AresValley/ENIGMA/rotors/400009/README.md

<!-- PROJECT LOGO -->
<p align="center">
  <a href="https://github.com/AresValley/ENIGMA">
    
  </a>
</p>

<!-- ABOUT THE PROJECT -->
## Center Toothed Wheel - 400 009

**ID:** 400009 <br/>
**Material:** [PA6](https://github.com/AresValley/ENIGMA#pa6-) <br/>
**Weight:** 34.5 g <br/>
**A360:** https://a360.co/4fqHECO <br/>

### Blueprint
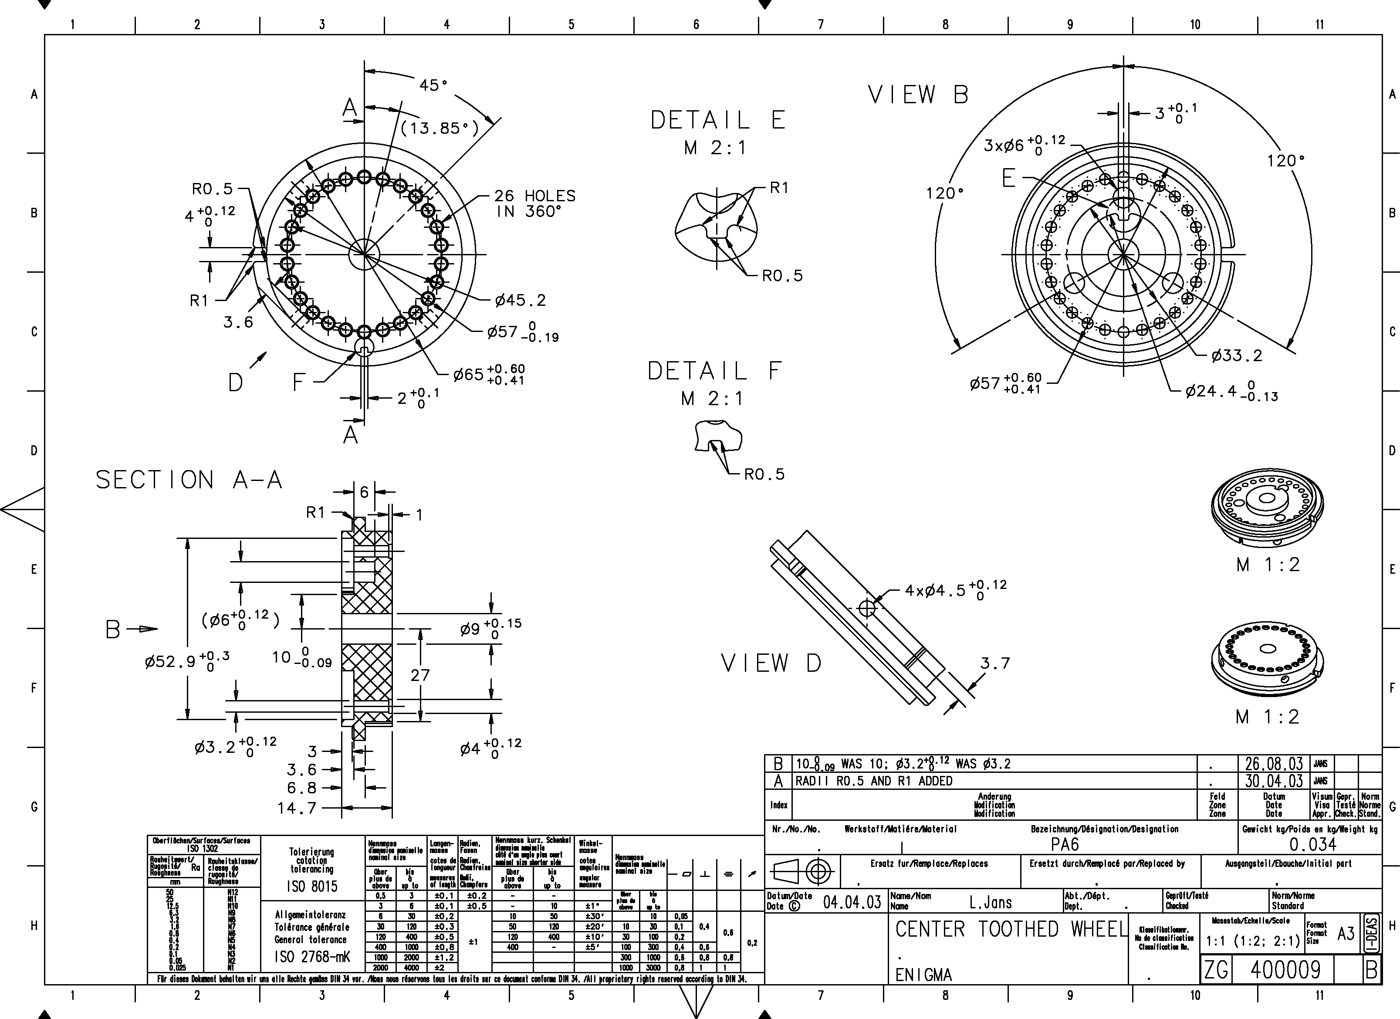
[picture p27: rotors/400009/BP.png]
Blueprint
