AresValley/ENIGMA/rotors/400012/README.md

<!-- PROJECT LOGO -->
<p align="center">
  <a href="https://github.com/AresValley/ENIGMA">
    
  </a>
</p>

<!-- ABOUT THE PROJECT -->
## STEEL BUSHING - 400 012

**ID:** 400012 <br/>
**Material:** [S235JR](https://github.com/AresValley/ENIGMA#s235jr-) <br/>
**Weight:** 8.37 g <br/>
**A360:** https://a360.co/3UYaBhf <br/>

### Blueprint
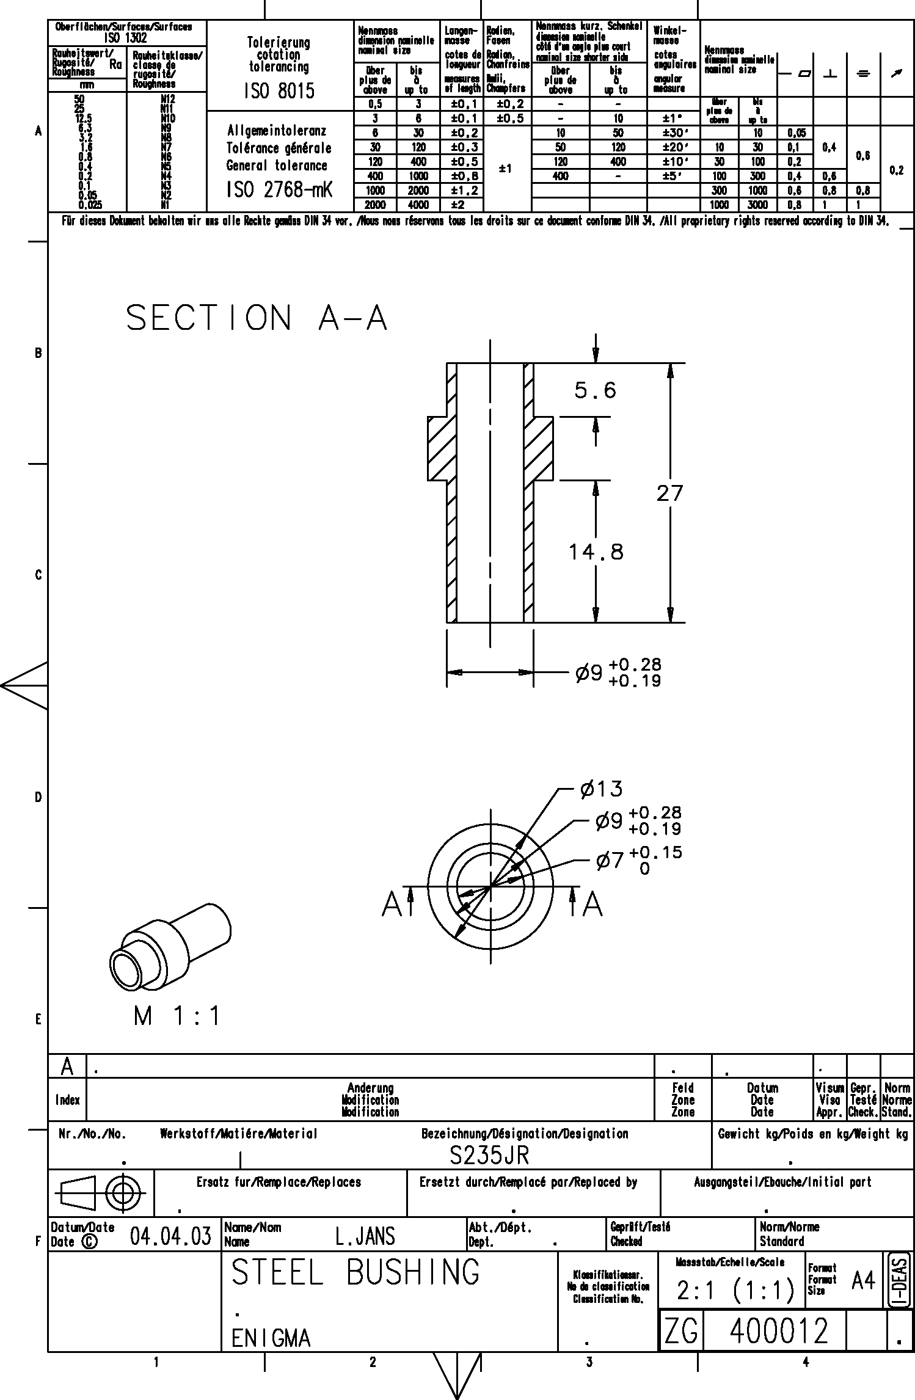
[picture p28: rotors/400012/BP.png]
