AresValley/ENIGMA/rack/100001/README.md

<!-- PROJECT LOGO -->
<p align="center">
  <a href="https://github.com/AresValley/ENIGMA">
    
  </a>
</p>

<!-- ABOUT THE PROJECT -->
## BEARING BLOCK LEFT - 100 001

**ID:** 100001 <br/>
**Material:** [S235JR](https://github.com/AresValley/ENIGMA#s235jr-) <br/>
**Weight:** 0.155 Kg <br/>
**A360:** https://a360.co/2P5f7vf <br/>

### Blueprint
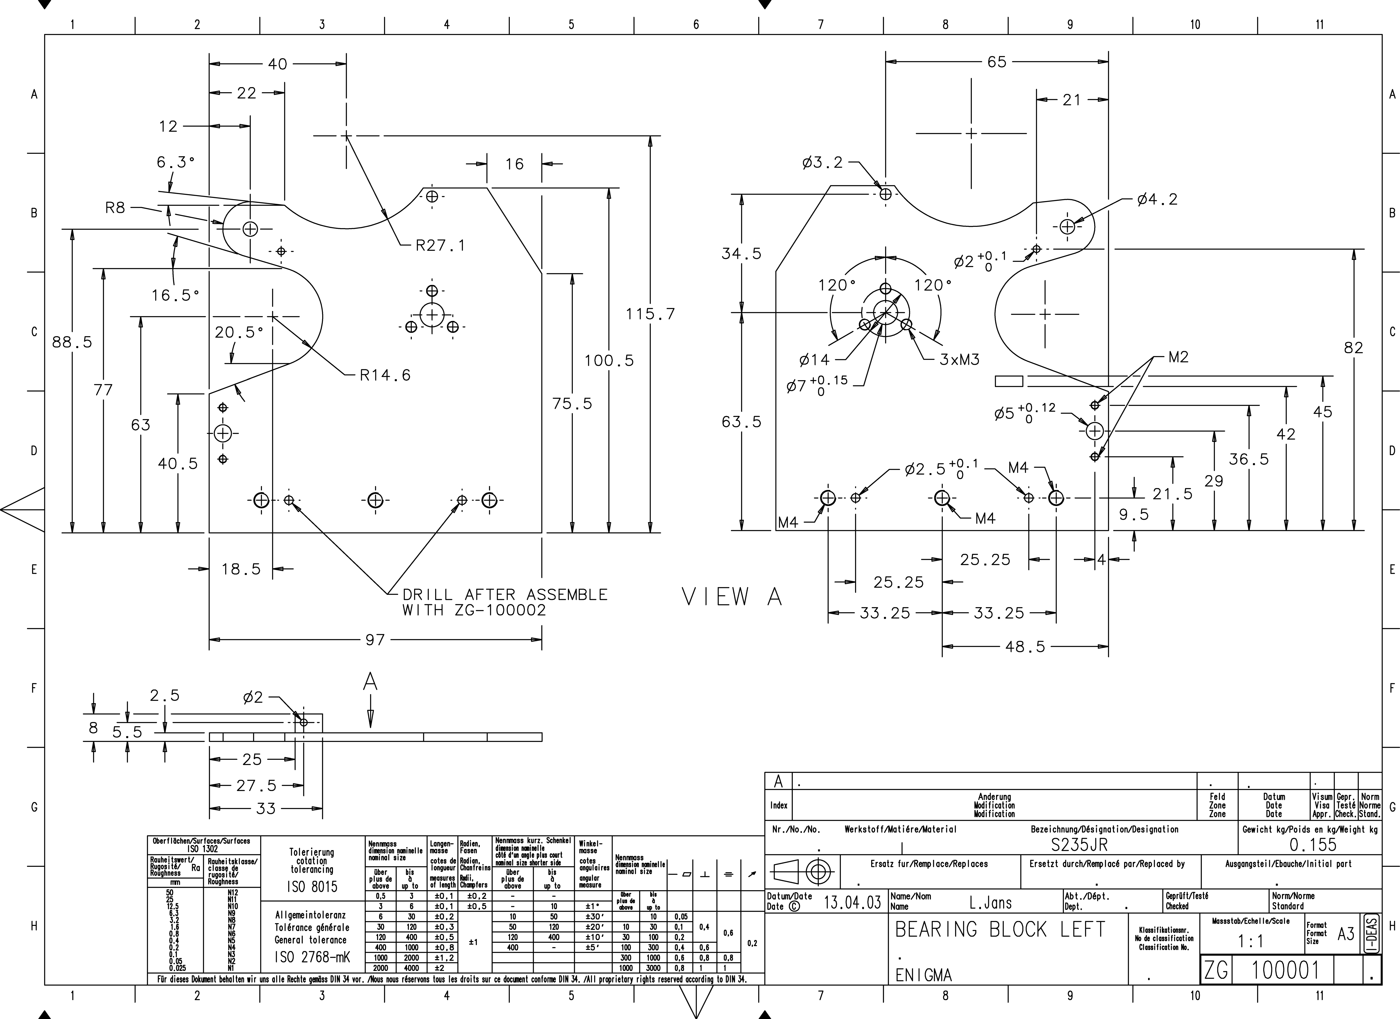
[picture p29: rack/100001/BP.png]
Blueprint
