AresValley/ENIGMA/rack/100005/README.md

<!-- PROJECT LOGO -->
<p align="center">
  <a href="https://github.com/AresValley/ENIGMA">
    
  </a>
</p>

<!-- ABOUT THE PROJECT -->
## SHAFT HOLDER - 100 005

**ID:** 100005 <br/>
**Material:** [S235JR](https://github.com/AresValley/ENIGMA#s235jr-) <br/>
**Weight:** 19.14 g <br/>
**A360:** https://a360.co/3PCjWI3 <br/>

### Blueprint
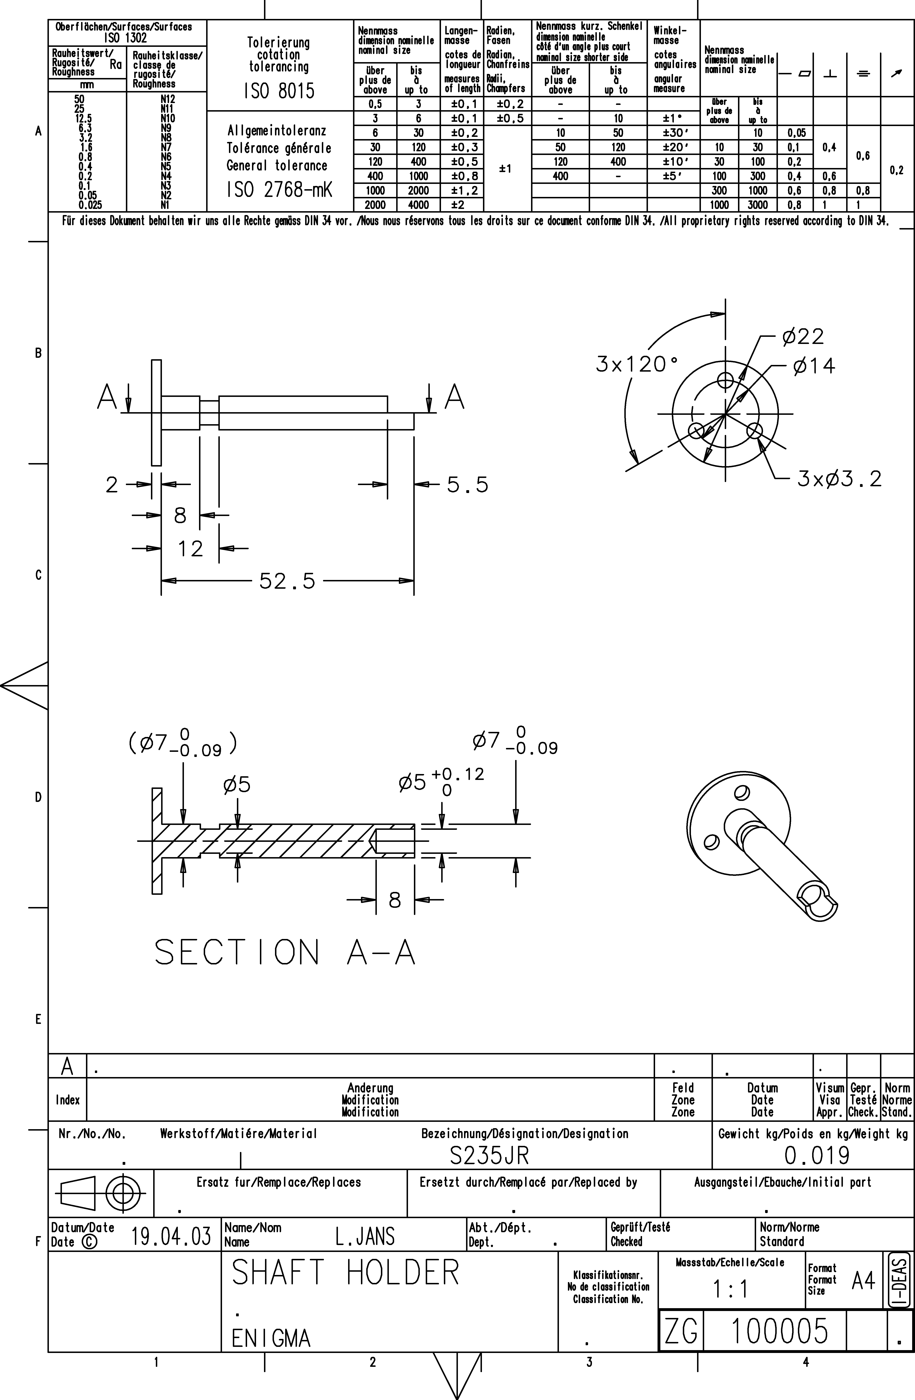
[picture p30: rack/100005/BP.png]
