AresValley/ENIGMA/rotors/400013/README.md

<!-- PROJECT LOGO -->
<p align="center">
  <a href="https://github.com/AresValley/ENIGMA">
    
  </a>
</p>

<!-- ABOUT THE PROJECT -->
## THREAD BUSHING - 400 013

**ID:** 400013 <br/>
**Material:** [S235JR](https://github.com/AresValley/ENIGMA#s235jr-) <br/>
**Weight:** 1.1 g <br/>
**A360:** https://a360.co/3PBEhyj <br/>

### Blueprint
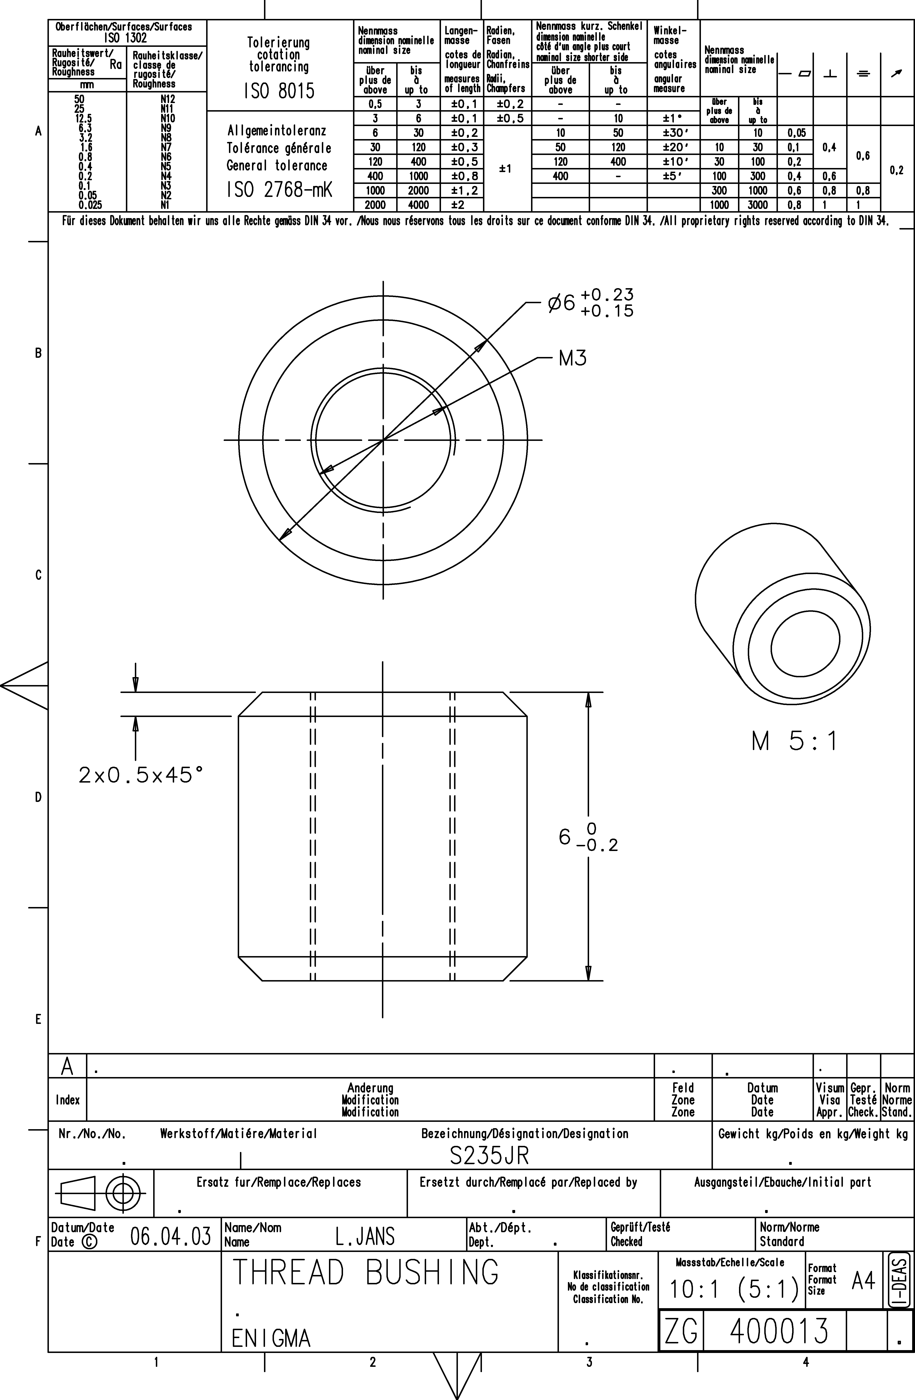
[picture p31: rotors/400013/BP.png]
