AresValley/ENIGMA/rotors/400017/README.md

<!-- PROJECT LOGO -->
<p align="center">
  <a href="https://github.com/AresValley/ENIGMA">
    
  </a>
</p>

<!-- ABOUT THE PROJECT -->
## SPRING - 400 017

**ID:** 400017 <br/>
**Material:** [CuZn40](https://github.com/AresValley/ENIGMA#cuzn40-) <br/>
**Weight:** 0.02 g <br/>
**A360:** https://a360.co/3RgDBjn <br/>

### Blueprint
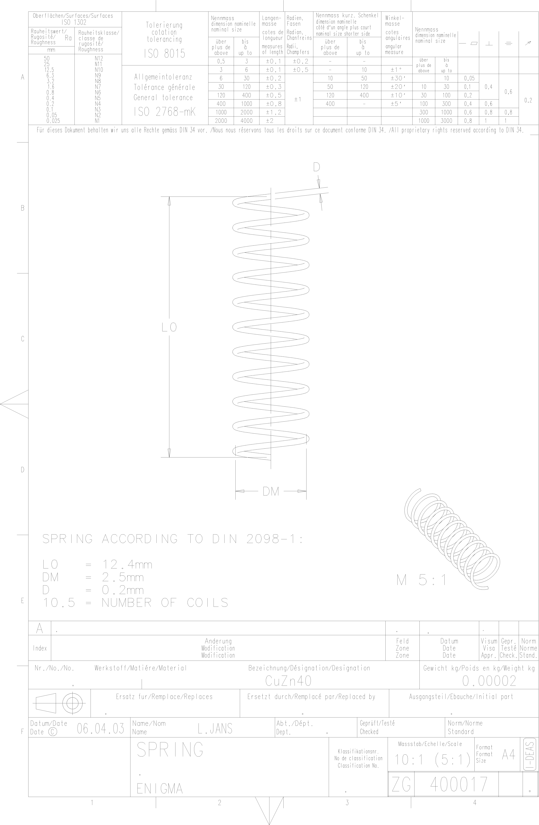
[picture p32: rotors/400017/BP.png]
