AresValley/ENIGMA/rotors/400019/README.md

<!-- PROJECT LOGO -->
<p align="center">
  <a href="https://github.com/AresValley/ENIGMA">
    
  </a>
</p>

<!-- ABOUT THE PROJECT -->
## THREAD BUSHING SMALL - 400 019

**ID:** 400019 <br/>
**Material:** [S235JR](https://github.com/AresValley/ENIGMA#s235jr-) <br/>
**Weight:** 0.38 g <br/>
**A360:** https://a360.co/45SvyxI <br/>

### Blueprint
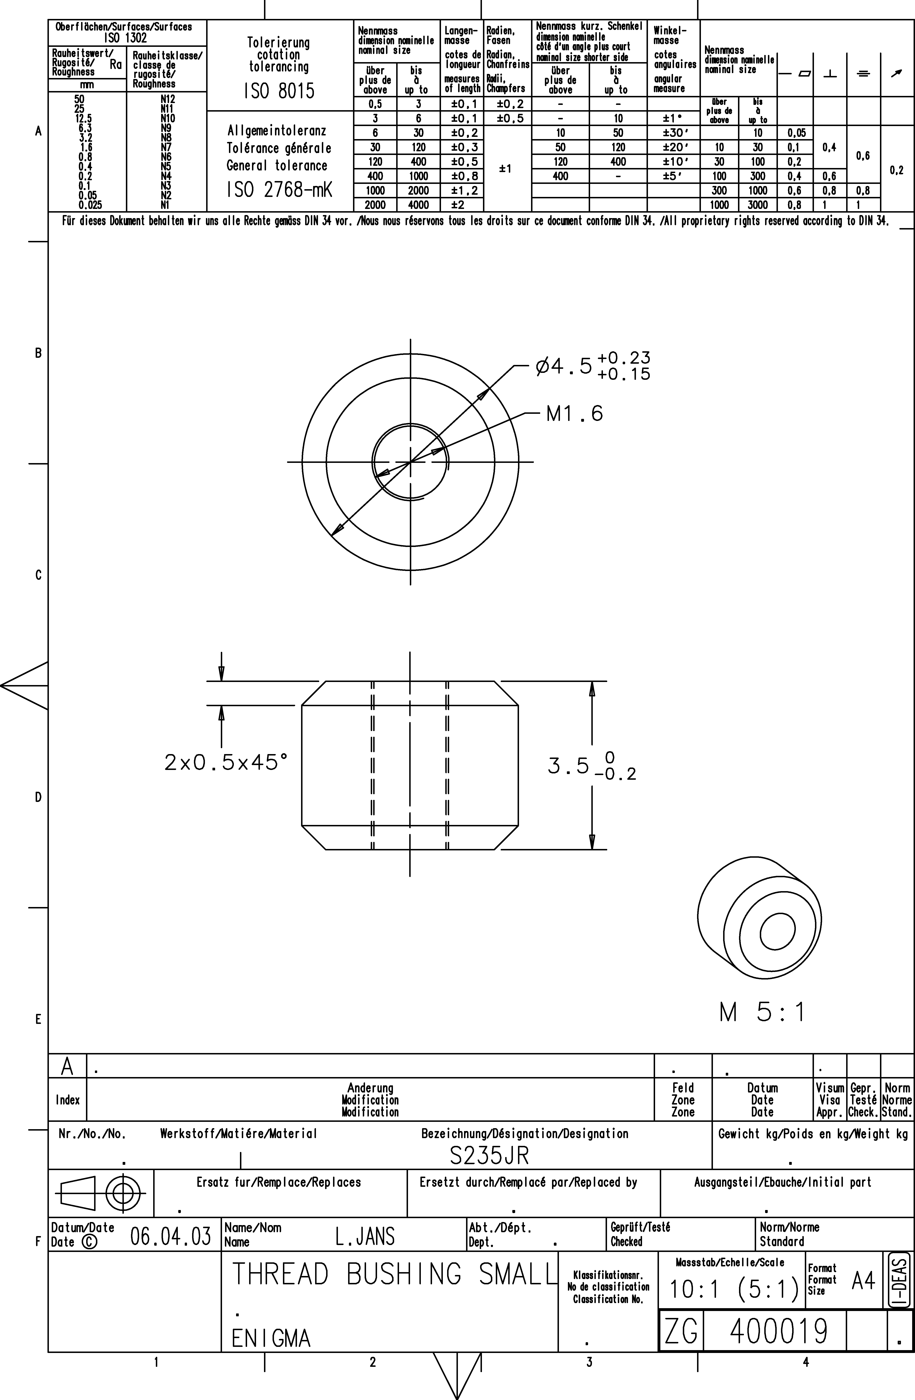
[picture p33: rotors/400019/BP.png]
