AresValley/ENIGMA/rotors/400001/README.md

<!-- PROJECT LOGO -->
<p align="center">
  <a href="https://github.com/AresValley/ENIGMA">
    
  </a>
</p>

<!-- ABOUT THE PROJECT -->
## KERFRING - 400 001

**ID:** 400001 <br/>
**Material:** [S235JR](https://github.com/AresValley/ENIGMA#s235jr-) <br/>
**Weight:** 0.0169 Kg <br/>
**A360:** https://a360.co/2ZTC5rj <br/>

### Blueprint
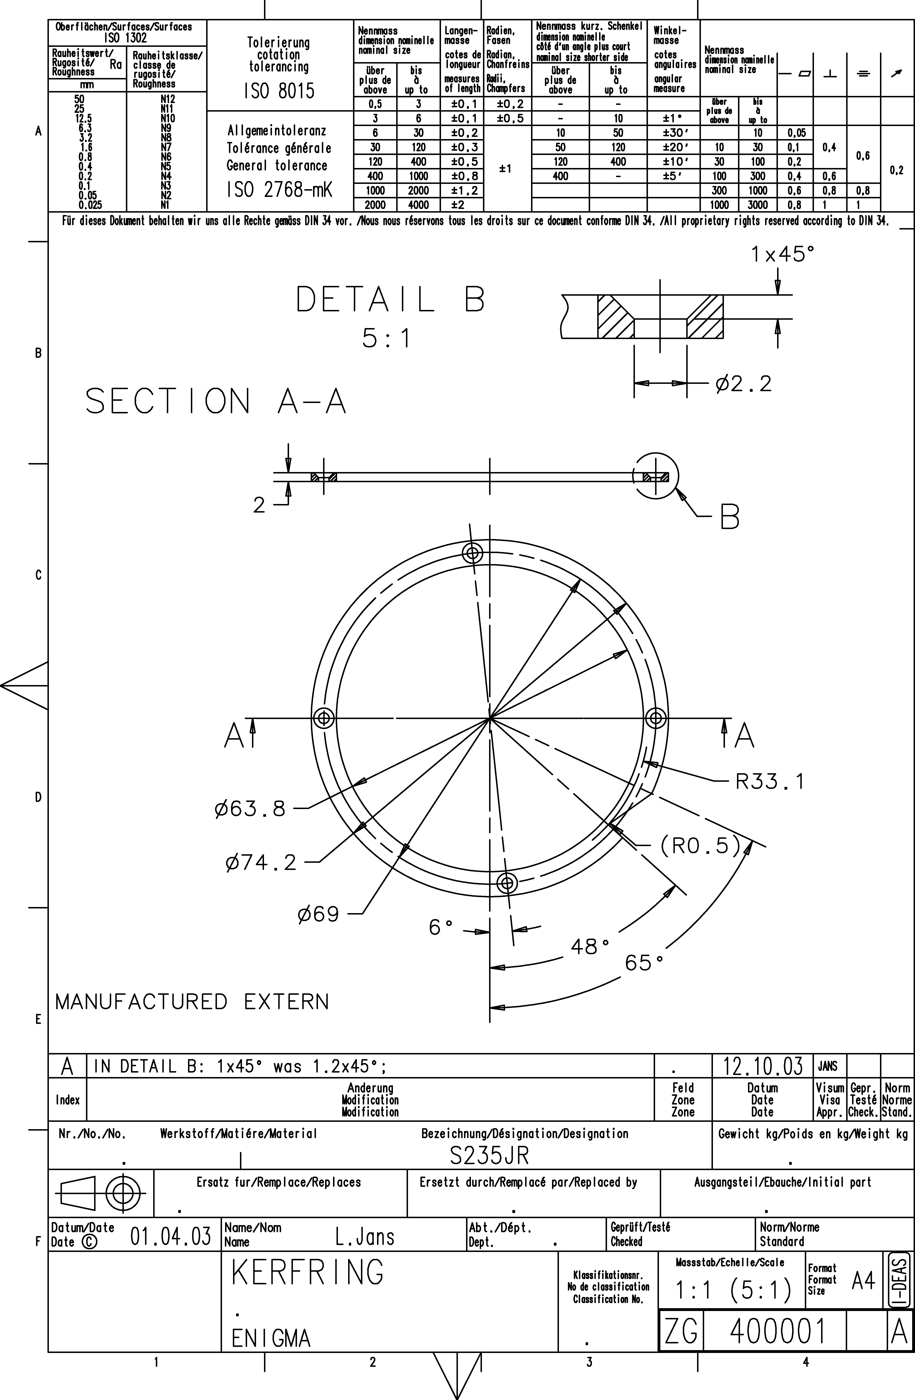
[picture p34: rotors/400001/BP.png]
