AresValley/ENIGMA/rotors/400002/README.md

<!-- PROJECT LOGO -->
<p align="center">
  <a href="https://github.com/AresValley/ENIGMA">
    
  </a>
</p>

<!-- ABOUT THE PROJECT -->
## DIGITRING - 400 002

**ID:** 400002 <br/>
**Material:** [S235JR](https://github.com/AresValley/ENIGMA#x12cr13-) <br/>
**Weight:** 0.113 Kg <br/>
**A360:** https://a360.co/3kyzwol <br/>

### Blueprint
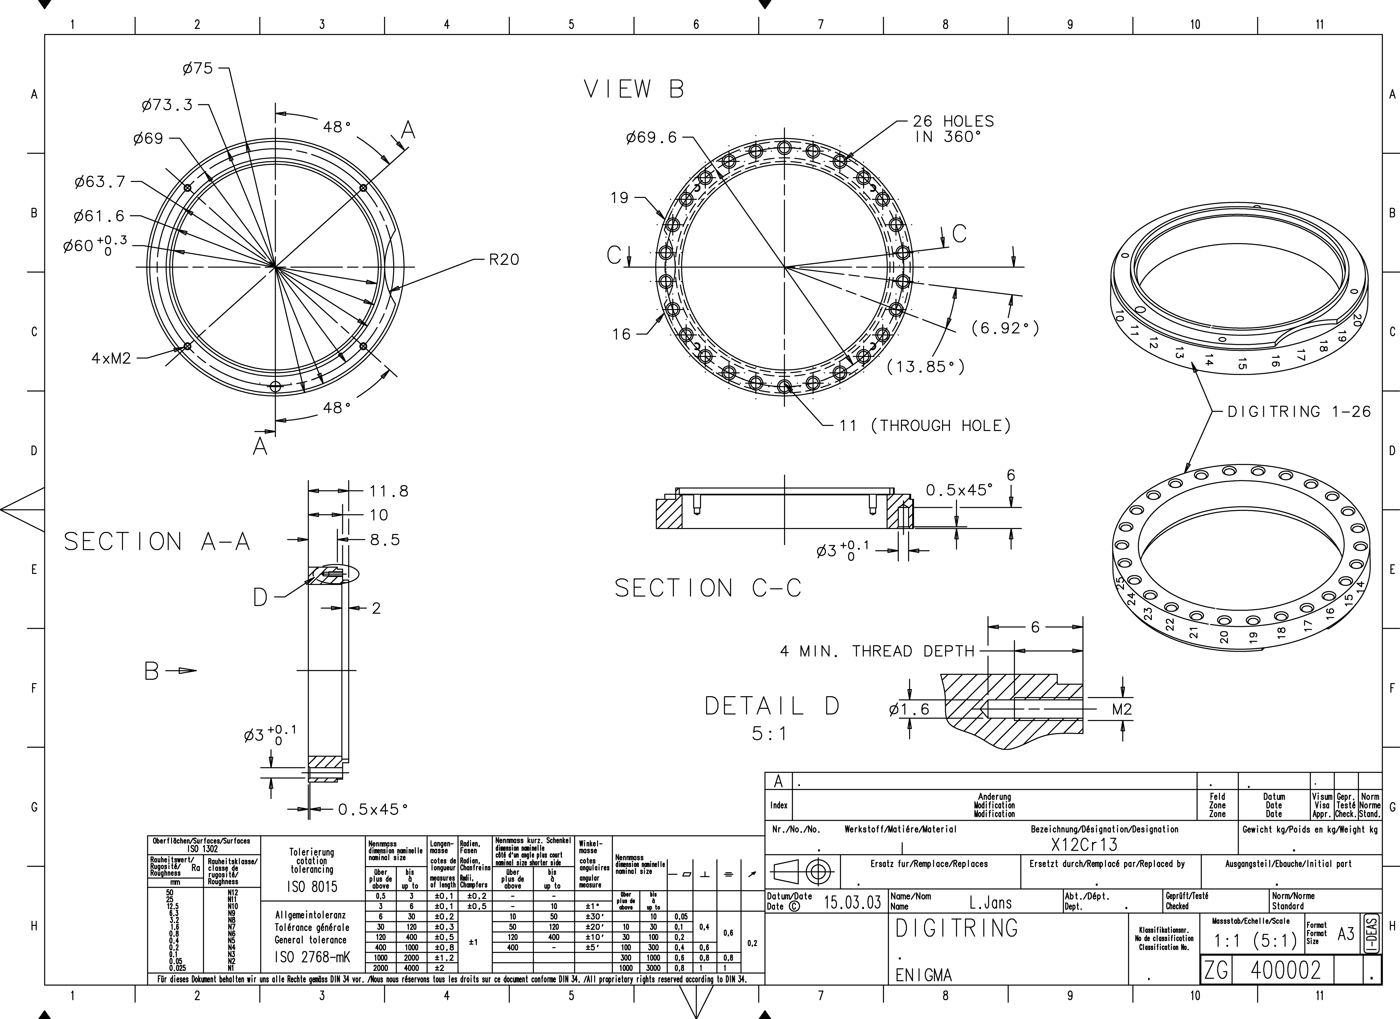
[picture p35: rotors/400002/BP.png]
