AresValley/ENIGMA/rotors/400003/README.md

<!-- PROJECT LOGO -->
<p align="center">
  <a href="https://github.com/AresValley/ENIGMA">
    
  </a>
</p>

<!-- ABOUT THE PROJECT -->
## BUSHING - 400 003

**ID:** 400003 <br/>
**Material:** [S235JR](https://github.com/AresValley/ENIGMA#s235jr-) <br/>
**Weight:** 0.054 Kg <br/>
**A360:** https://a360.co/3sJqWpV <br/>

### Blueprint
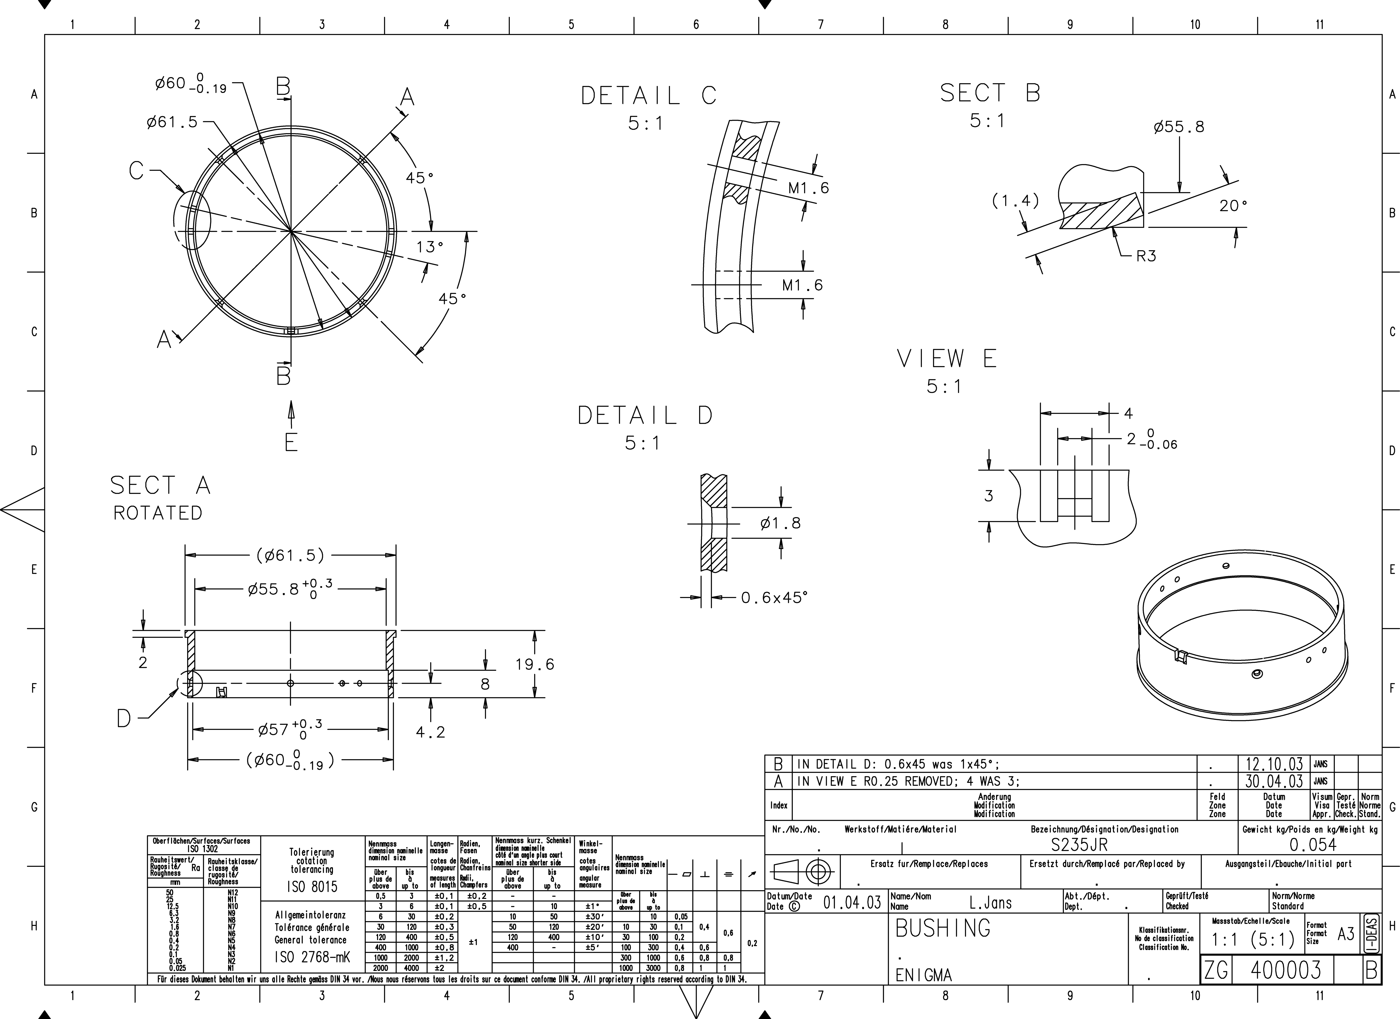
[picture p36: rotors/400003/BP.png]
