AresValley/ENIGMA/rotors/400004/README.md

<!-- PROJECT LOGO -->
<p align="center">
  <a href="https://github.com/AresValley/ENIGMA">
    
  </a>
</p>

<!-- ABOUT THE PROJECT -->
## ROLL SHAFT - 400 004

**ID:** 400004 <br/>
**Material:** [S235JR](https://github.com/AresValley/ENIGMA#s235jr-) <br/>
**Weight:** 0.0270 Kg <br/>
**A360:** https://a360.co/2NRQIZV <br/>

### Blueprint
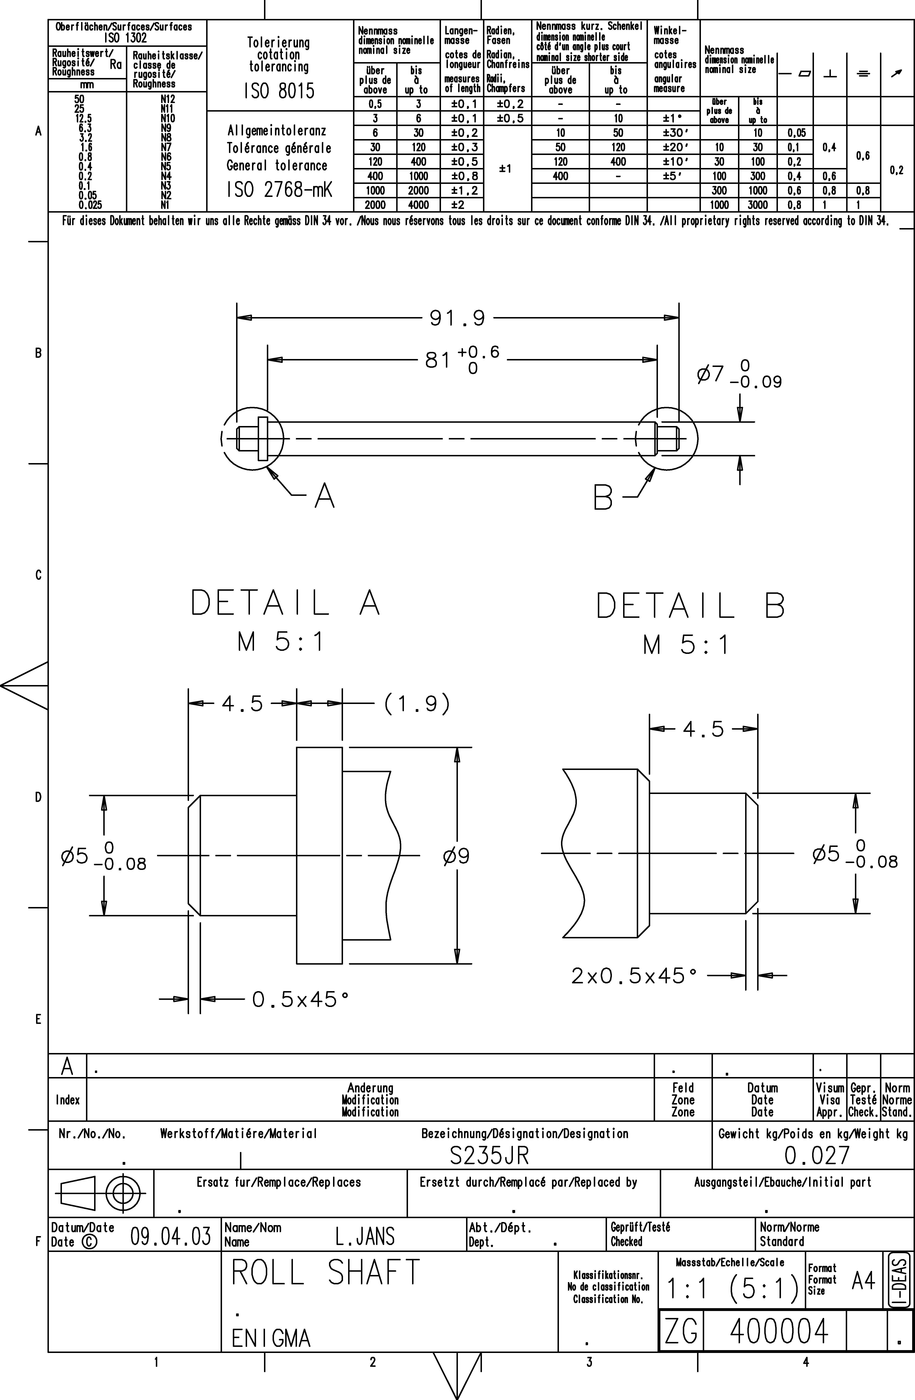
[picture p37: rotors/400004/BP.png]
