AresValley/ENIGMA/rotors/400005/README.md

<!-- PROJECT LOGO -->
<p align="center">
  <a href="https://github.com/AresValley/ENIGMA">
    
  </a>
</p>

<!-- ABOUT THE PROJECT -->
## BRACKET - 400 005

**ID:** 400005 <br/>
**Material:** [S235JR](https://github.com/AresValley/ENIGMA#s235jr-) <br/>
**Weight:** 0.0020 Kg <br/>
**A360:** https://a360.co/3lvvoXo <br/>

### Blueprint
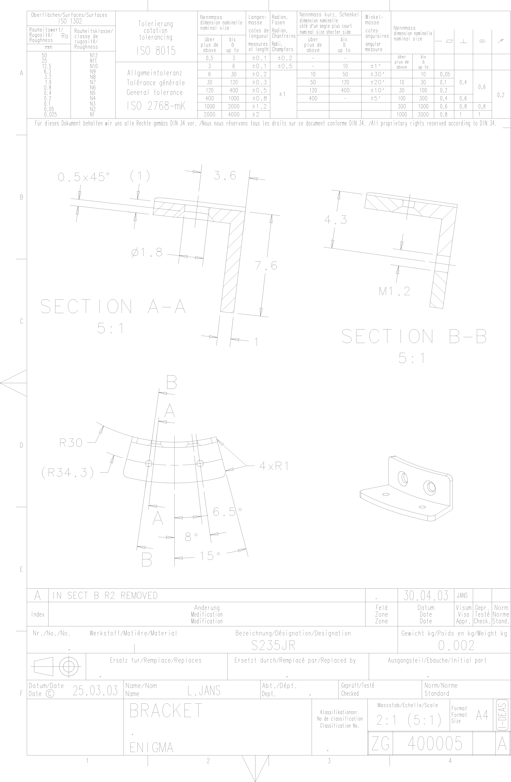
[picture p38: rotors/400005/BP.png]
