AresValley/ENIGMA/rotors/400006/README.md

<!-- PROJECT LOGO -->
<p align="center">
  <a href="https://github.com/AresValley/ENIGMA">
    
  </a>
</p>

<!-- ABOUT THE PROJECT -->
## CLAMP - 400 006

**ID:** 400006 <br/>
**Material:** [38Si7](https://github.com/AresValley/ENIGMA#38si7-) <br/>
**Weight:** 0.0013 Kg <br/>
**A360:** https://a360.co/3wWaZkC <br/>

### Blueprint
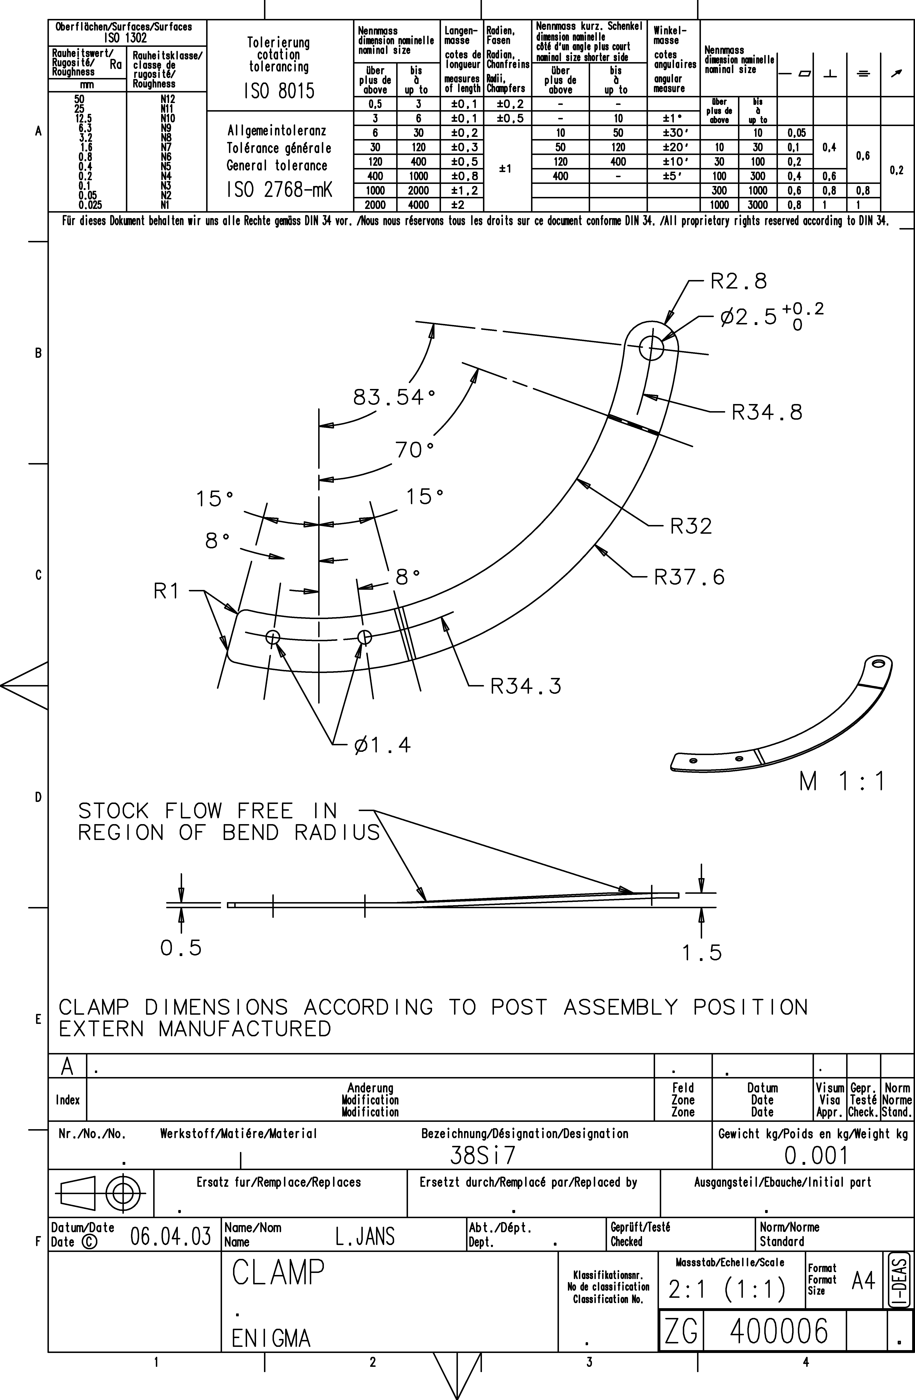
[picture p39: rotors/400006/BP.png]
