AresValley/ENIGMA/rotors/400007/README.md

<!-- PROJECT LOGO -->
<p align="center">
  <a href="https://github.com/AresValley/ENIGMA">
    
  </a>
</p>

<!-- ABOUT THE PROJECT -->
## PIN - 400 007

**ID:** 400007 <br/>
**Material:** [S235JR](https://github.com/AresValley/ENIGMA#s235jr-) <br/>
**Weight:** 0.0004 Kg <br/>
**A360:** https://a360.co/385FHOT <br/>

### Blueprint
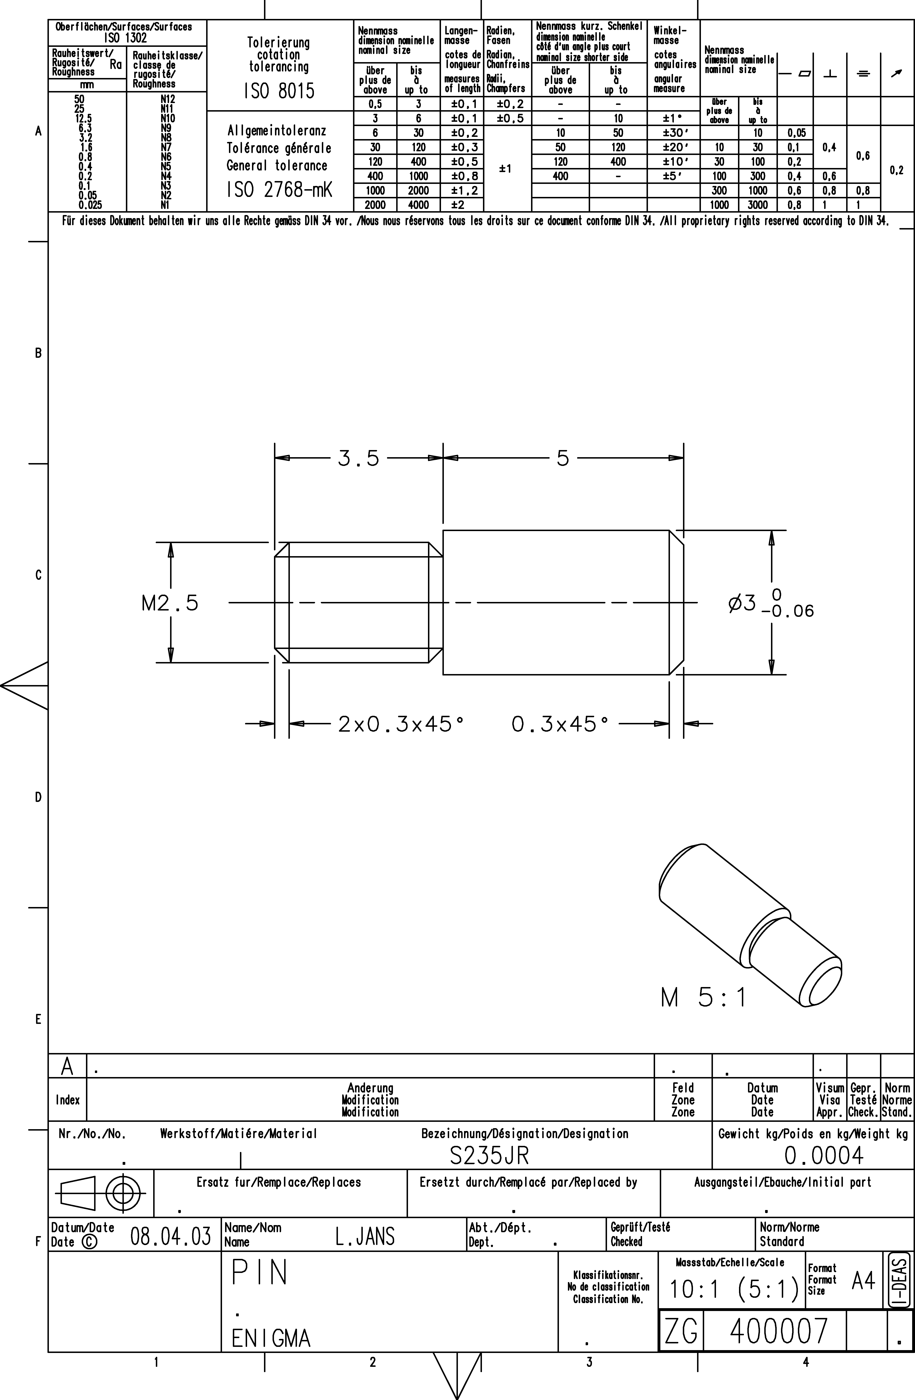
[picture p40: rotors/400007/BP.png]
