AresValley/ENIGMA/rotors/400011/README.md

<!-- PROJECT LOGO -->
<p align="center">
  <a href="https://github.com/AresValley/ENIGMA">
    
  </a>
</p>

<!-- ABOUT THE PROJECT -->
## ROLLPLATE - 400 011

**ID:** 400011 <br/>
**Material:** [PA6](https://github.com/AresValley/ENIGMA#pa6-) <br/>
**Weight:** 0.0090 Kg <br/>
**A360:** https://a360.co/3NFh4rl <br/>

### Blueprint
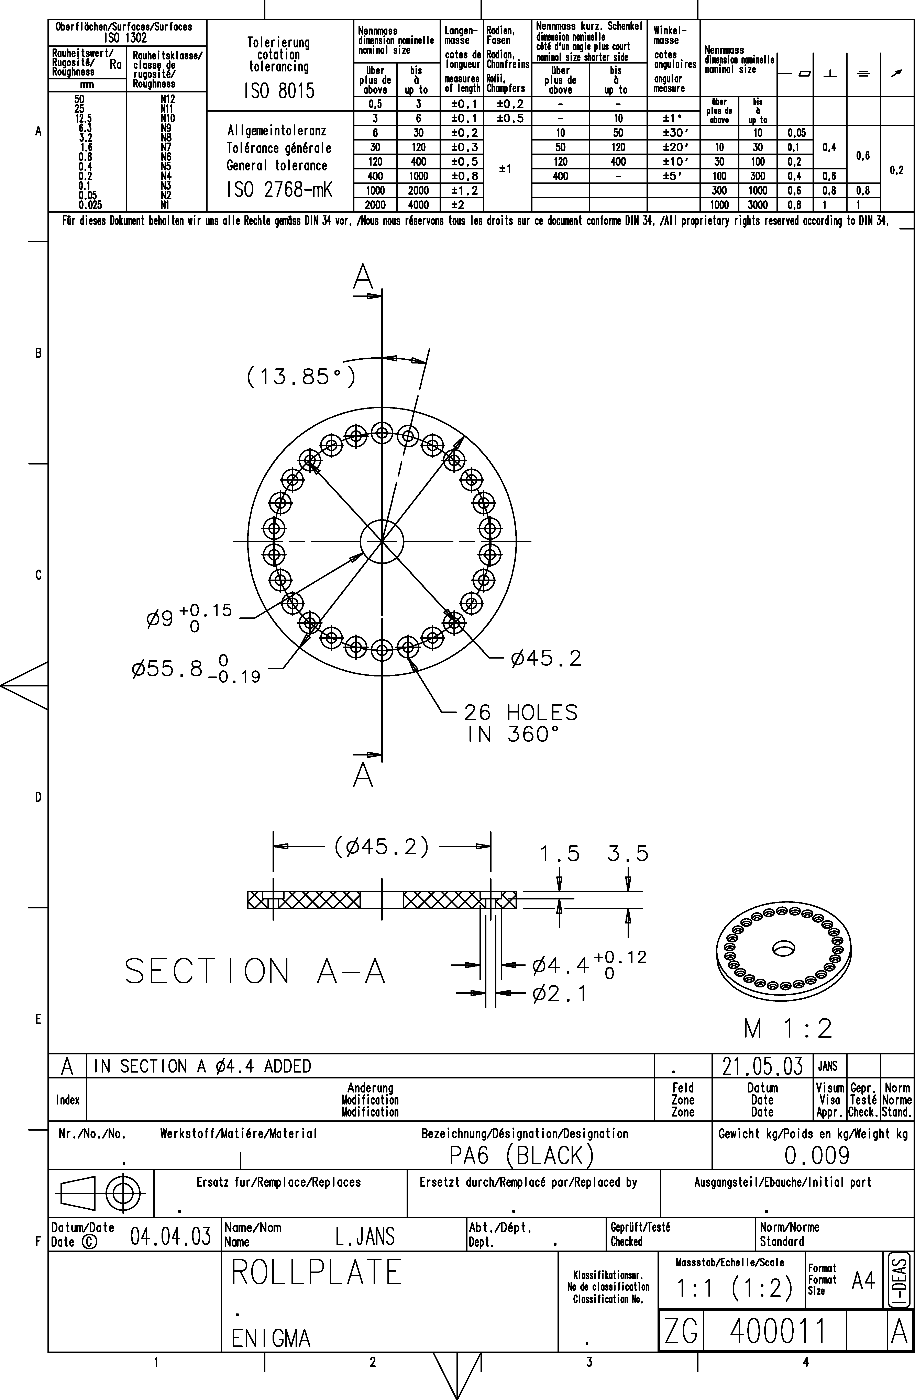
[picture p41: rotors/400011/BP.png]
