AresValley/ENIGMA/rotors/400014/README.md

<!-- PROJECT LOGO -->
<p align="center">
  <a href="https://github.com/AresValley/ENIGMA">
    
  </a>
</p>

<!-- ABOUT THE PROJECT -->
## THOOTED WHEEL - 400 014

**ID:** 400014 <br/>
**Material:** [S235JR](https://github.com/AresValley/ENIGMA#s235jr-) <br/>
**Weight:** 0.1140 Kg <br/>
**A360:** https://a360.co/38ouFV5 <br/>

### Blueprint
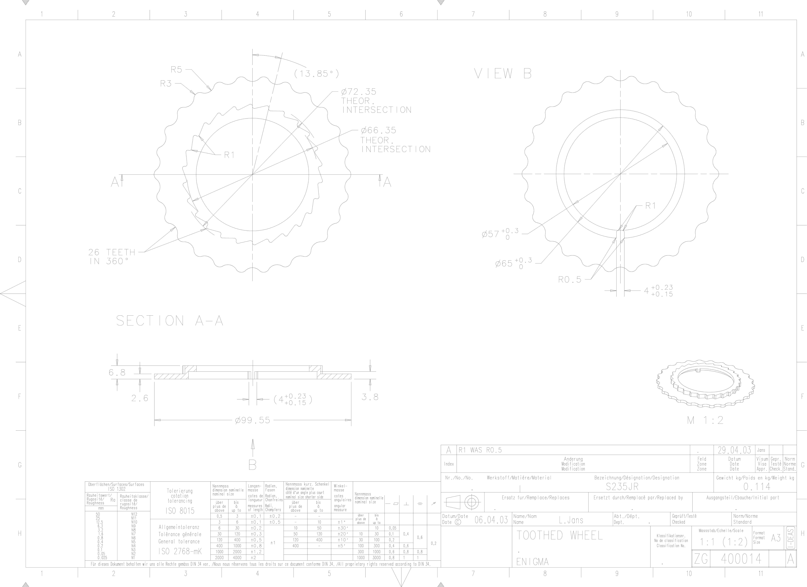
[picture p42: rotors/400014/BP.png]
