AresValley/ENIGMA/rotors/400016/README.md

<!-- PROJECT LOGO -->
<p align="center">
  <a href="https://github.com/AresValley/ENIGMA">
    
  </a>
</p>

<!-- ABOUT THE PROJECT -->
## CONTACT PIN - 400 016

**ID:** 400016 <br/>
**Material:** [CuZn40](https://github.com/AresValley/ENIGMA#cuzn40-) <br/>
**Weight:** 0.0003 Kg <br/>
**A360:** https://a360.co/3pN8evb <br/>

### Blueprint
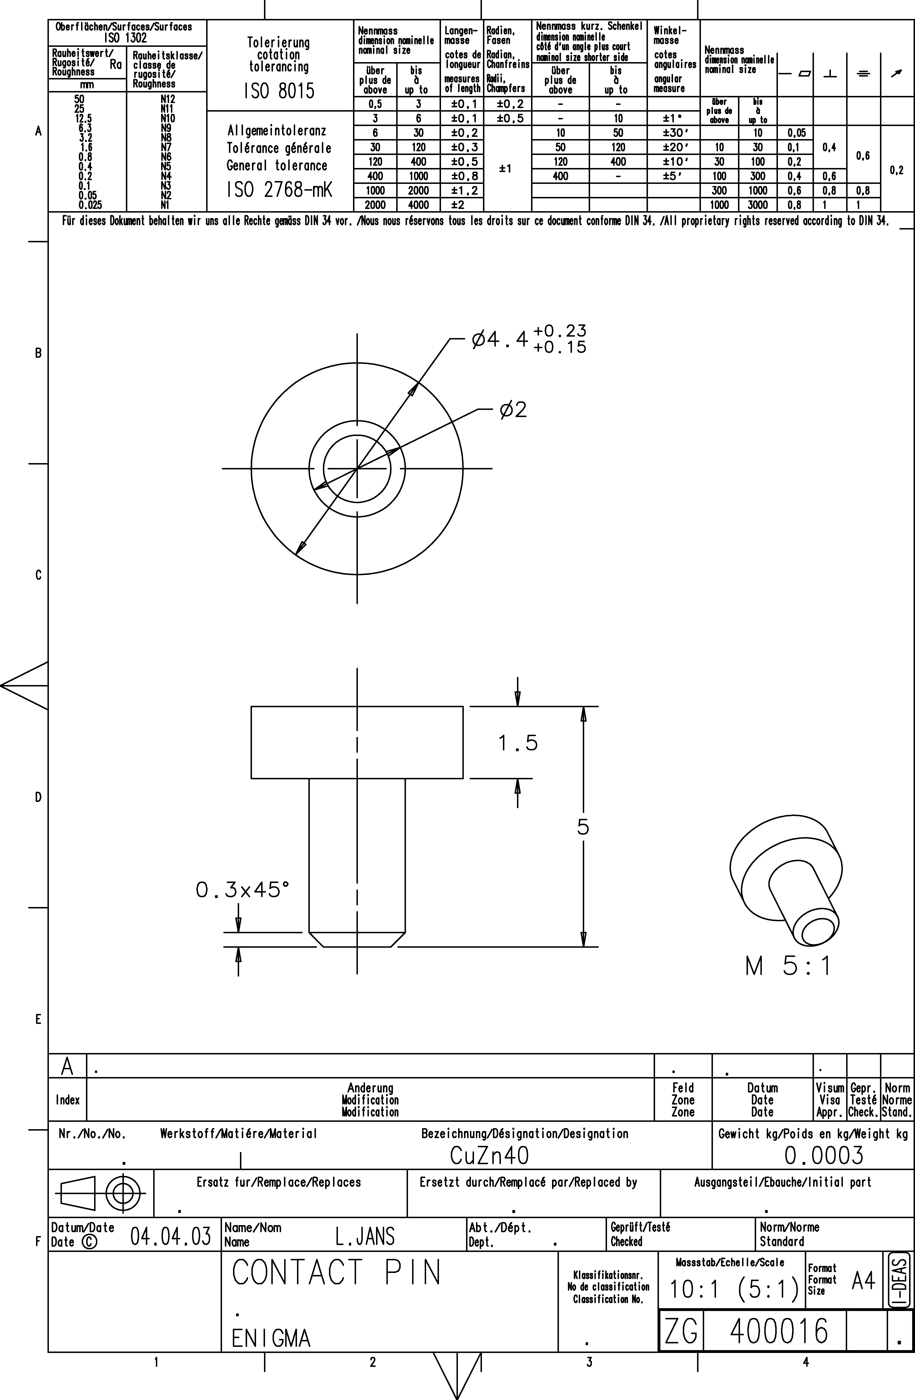
[picture p43: rotors/400016/BP.png]
Blueprint
