AresValley/ENIGMA/rotors/400018/README.md

<!-- PROJECT LOGO -->
<p align="center">
  <a href="https://github.com/AresValley/ENIGMA">
    
  </a>
</p>

<!-- ABOUT THE PROJECT -->
## SPRING PIN - 400 018

**ID:** 400018 <br/>
**Material:** [CuZn40](https://github.com/AresValley/ENIGMA#cuzn40-) <br/>
**Weight:** 0.0003 Kg <br/>
**A360:** https://a360.co/3kpOdtR <br/>

### Blueprint
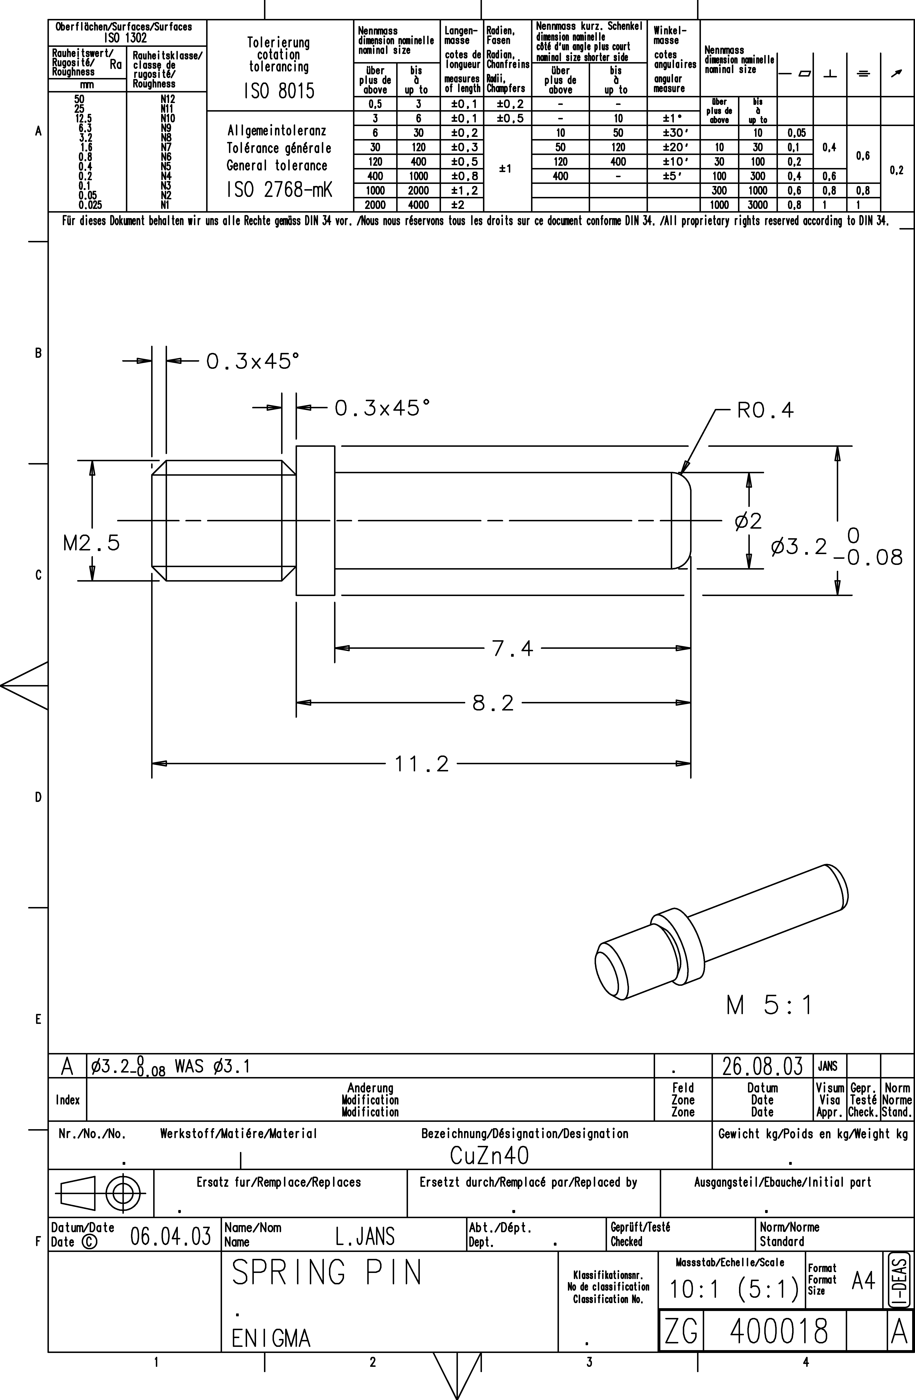
[picture p44: rotors/400018/BP.png]
Blueprint
