AresValley/ENIGMA/reflector/300008/README.md

<!-- PROJECT LOGO -->
<p align="center">
  <a href="https://github.com/AresValley/ENIGMA">
    
  </a>
</p>

<!-- ABOUT THE PROJECT -->
## ISOLATOR PLATE - 300 008

**ID:** 300008 <br/>
**Material:** [PA6](https://github.com/AresValley/ENIGMA#pa6) <br/>
**Weight:** 1.7 g <br/>
**A360:** https://a360.co/45IXvrc <br/>

### Blueprint
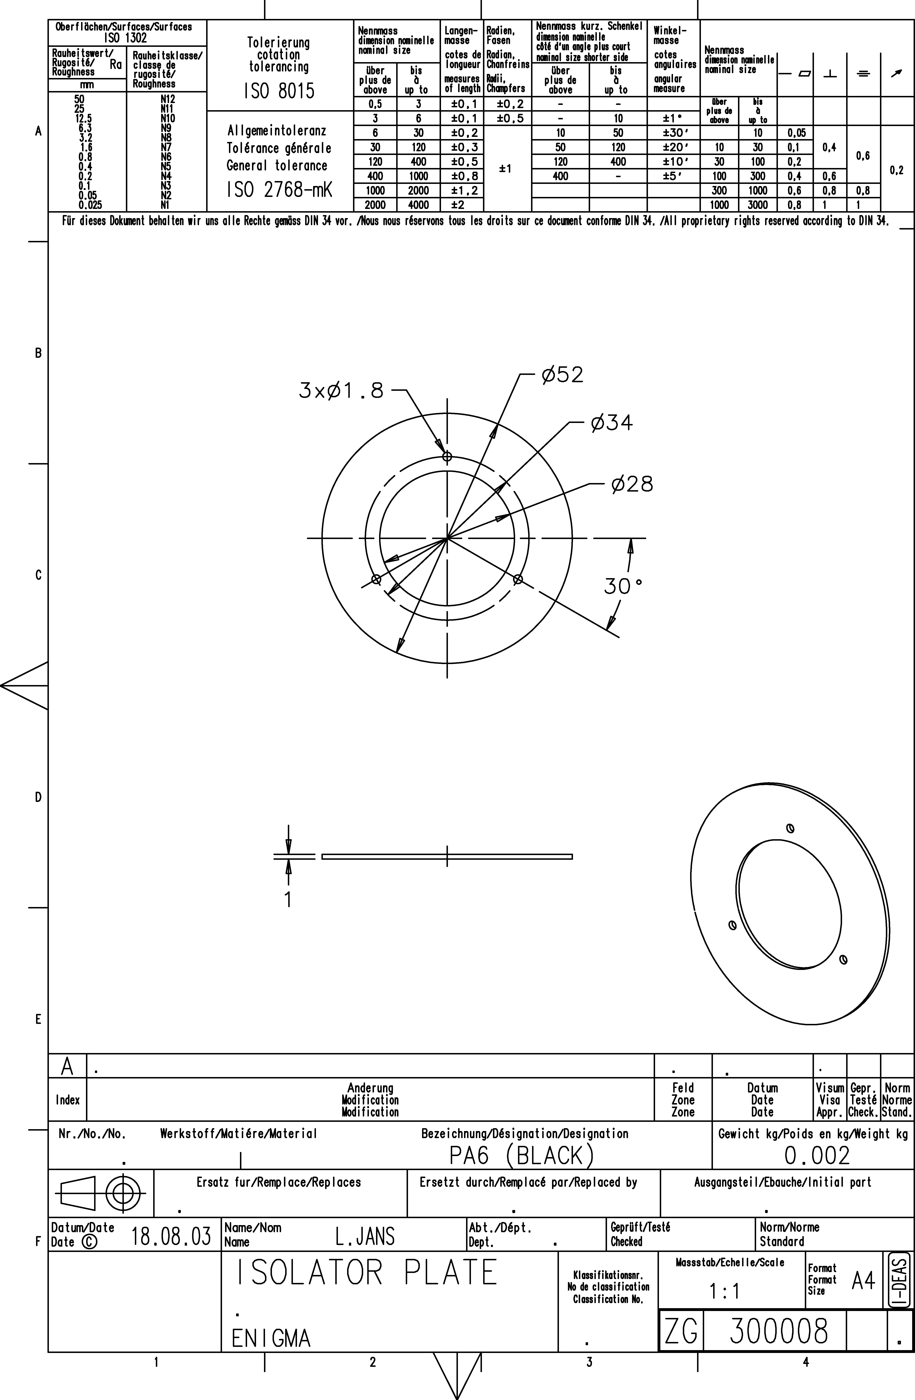
[picture p45: reflector/300008/BP.png]
Blueprint
