AresValley/ENIGMA/reflector/300007/README.md

<!-- PROJECT LOGO -->
<p align="center">
  <a href="https://github.com/AresValley/ENIGMA">
    
  </a>
</p>

<!-- ABOUT THE PROJECT -->
## SCREW PLATE - 300 007

**ID:** 300007 <br/>
**Material:** [S235JR](https://github.com/AresValley/ENIGMA#s235jr) <br/>
**Weight:** 1.4 g <br/>
**A360:** https://a360.co/45DTMM4 <br/>

### Blueprint
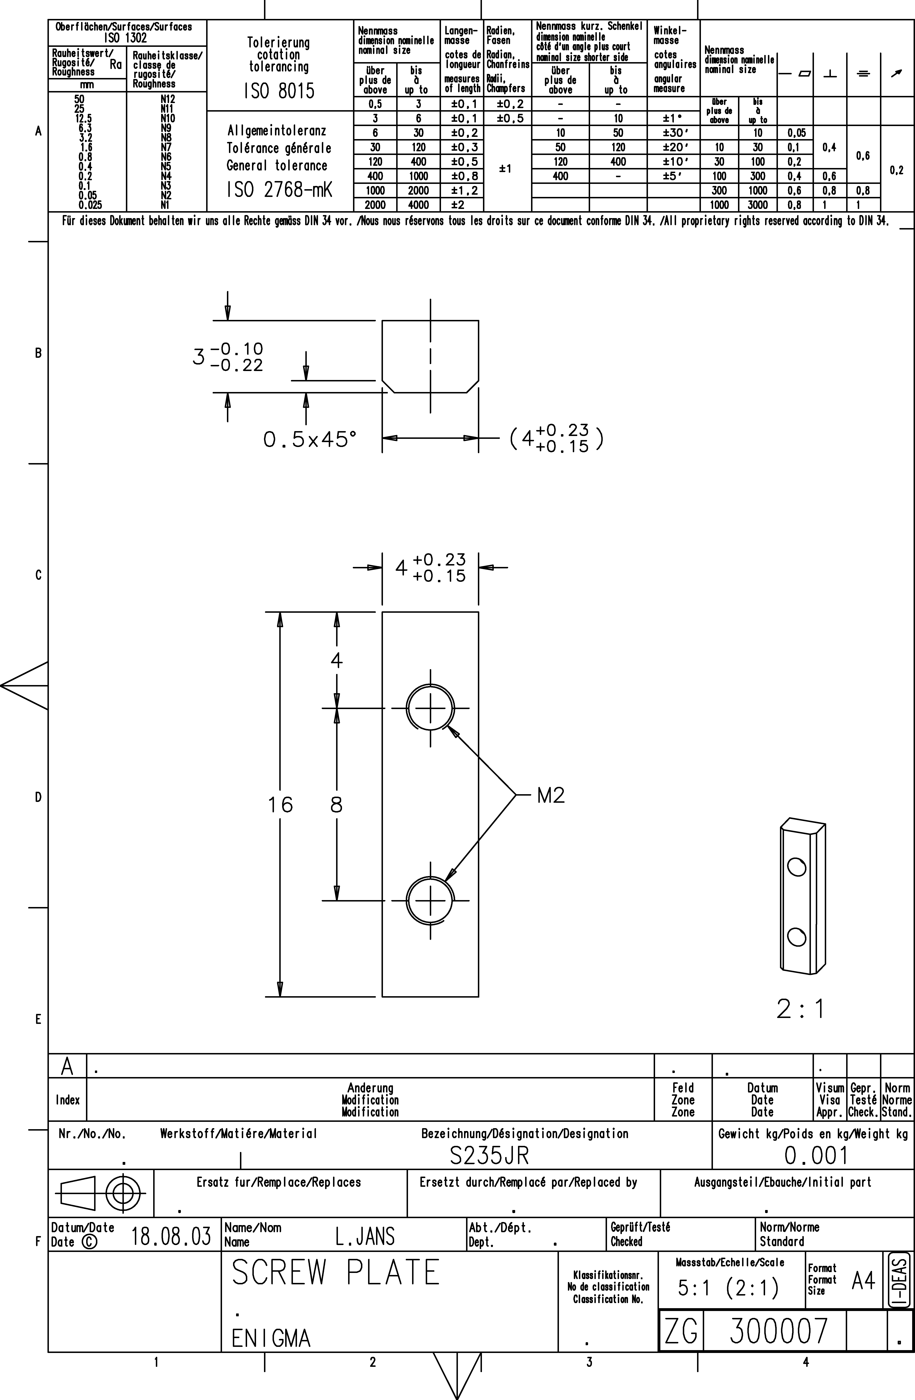
[picture p46: reflector/300007/BP.png]
Blueprint
