AresValley/ENIGMA/reflector/300009/README.md

<!-- PROJECT LOGO -->
<p align="center">
  <a href="https://github.com/AresValley/ENIGMA">
    
  </a>
</p>

<!-- ABOUT THE PROJECT -->
## AXLE - 300 009

**ID:** 300009 <br/>
**Material:** [S235JR](https://github.com/AresValley/ENIGMA#s235jr) <br/>
**Weight:** 4.5 g <br/>
**A360:** https://a360.co/3Z0qwfL <br/>

### Blueprint
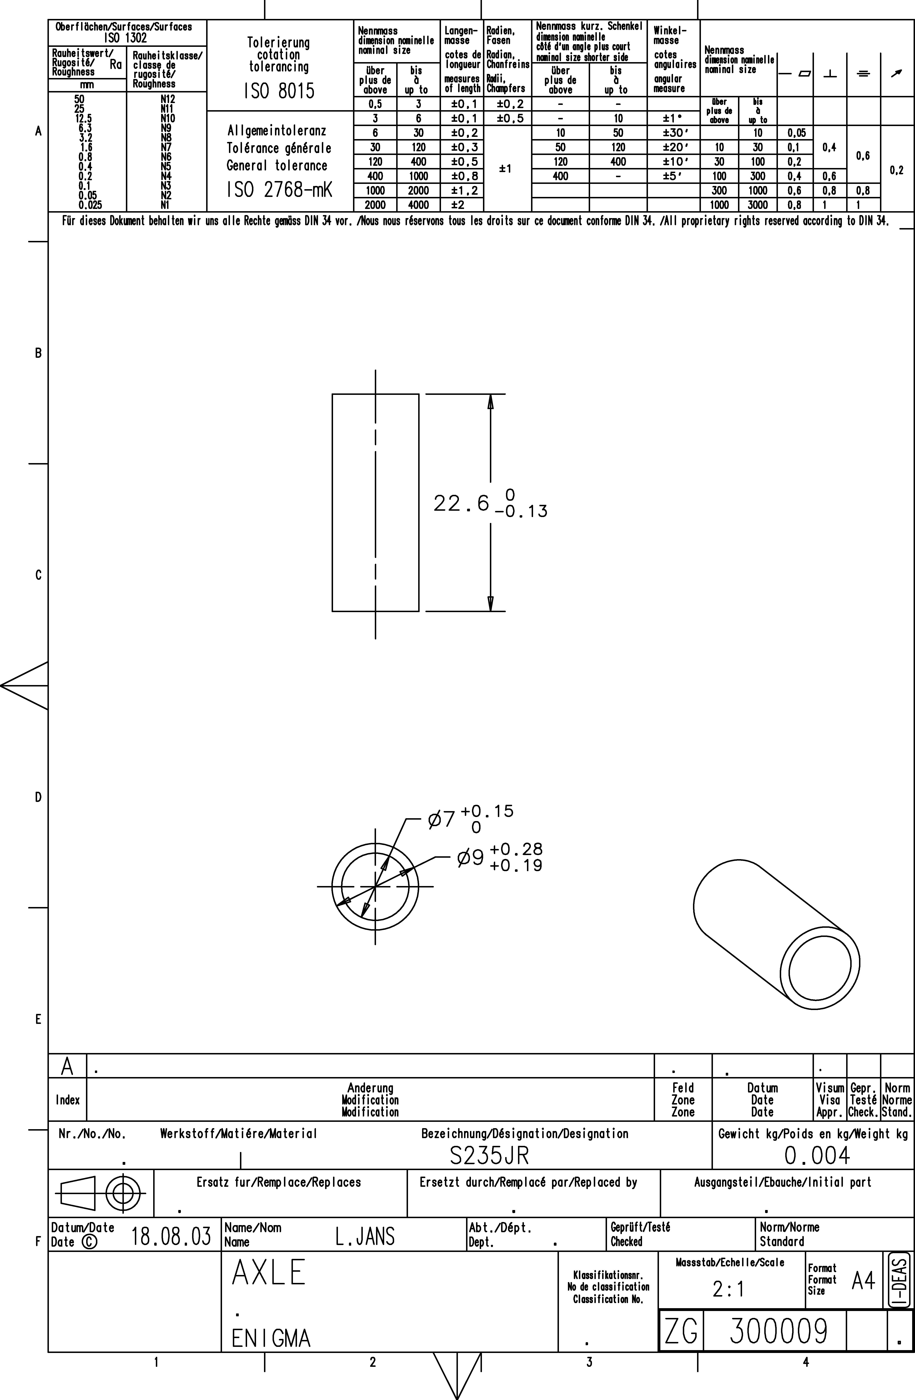
[picture p47: reflector/300009/BP.png]
Blueprint
