AresValley/ENIGMA/reflector/300006/README.md

<!-- PROJECT LOGO -->
<p align="center">
  <a href="https://github.com/AresValley/ENIGMA">
    
  </a>
</p>

<!-- ABOUT THE PROJECT -->
## BUSHING - 300 006

**ID:** 300006 <br/>
**Material:** [CuZn40](https://github.com/AresValley/ENIGMA#cuzn40) <br/>
**Weight:** 1.9 g <br/>
**A360:** https://a360.co/3qSZIS1 <br/>

### Blueprint
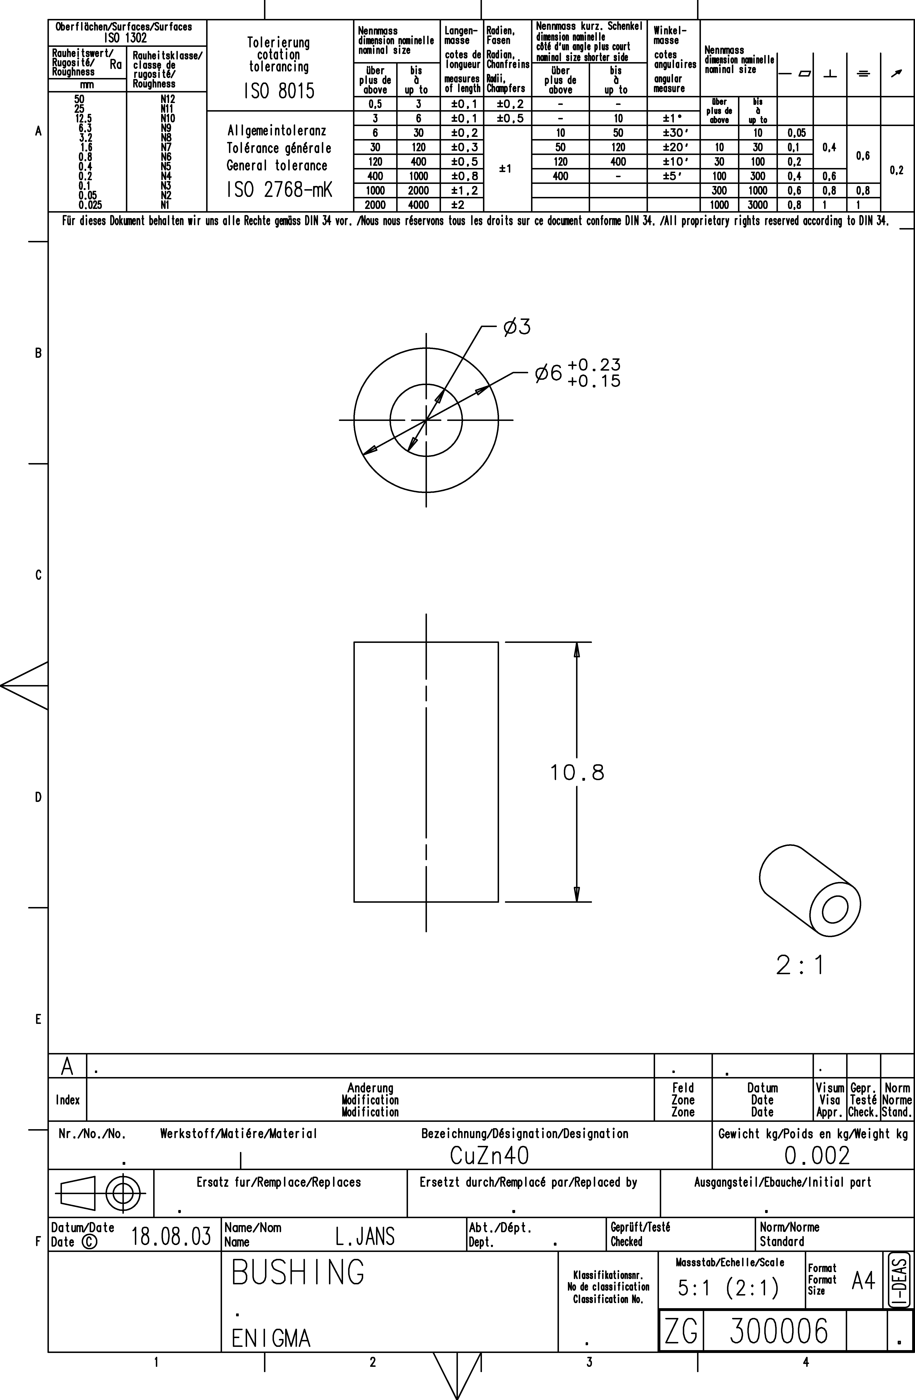
[picture p48: reflector/300006/BP.png]
Blueprint
