AresValley/ENIGMA/rotors/400008/README.md

<!-- PROJECT LOGO -->
<p align="center">
  <a href="https://github.com/AresValley/ENIGMA">
    
  </a>
</p>

<!-- ABOUT THE PROJECT -->
## CAP - 400 008

**ID:** 400008 <br/>
**Material:** [S235JR](https://github.com/AresValley/ENIGMA#s235jr-) <br/>
**Weight:** 0.37 g <br/>
**A360:** https://a360.co/3ALG7Iq <br/>

### Blueprint
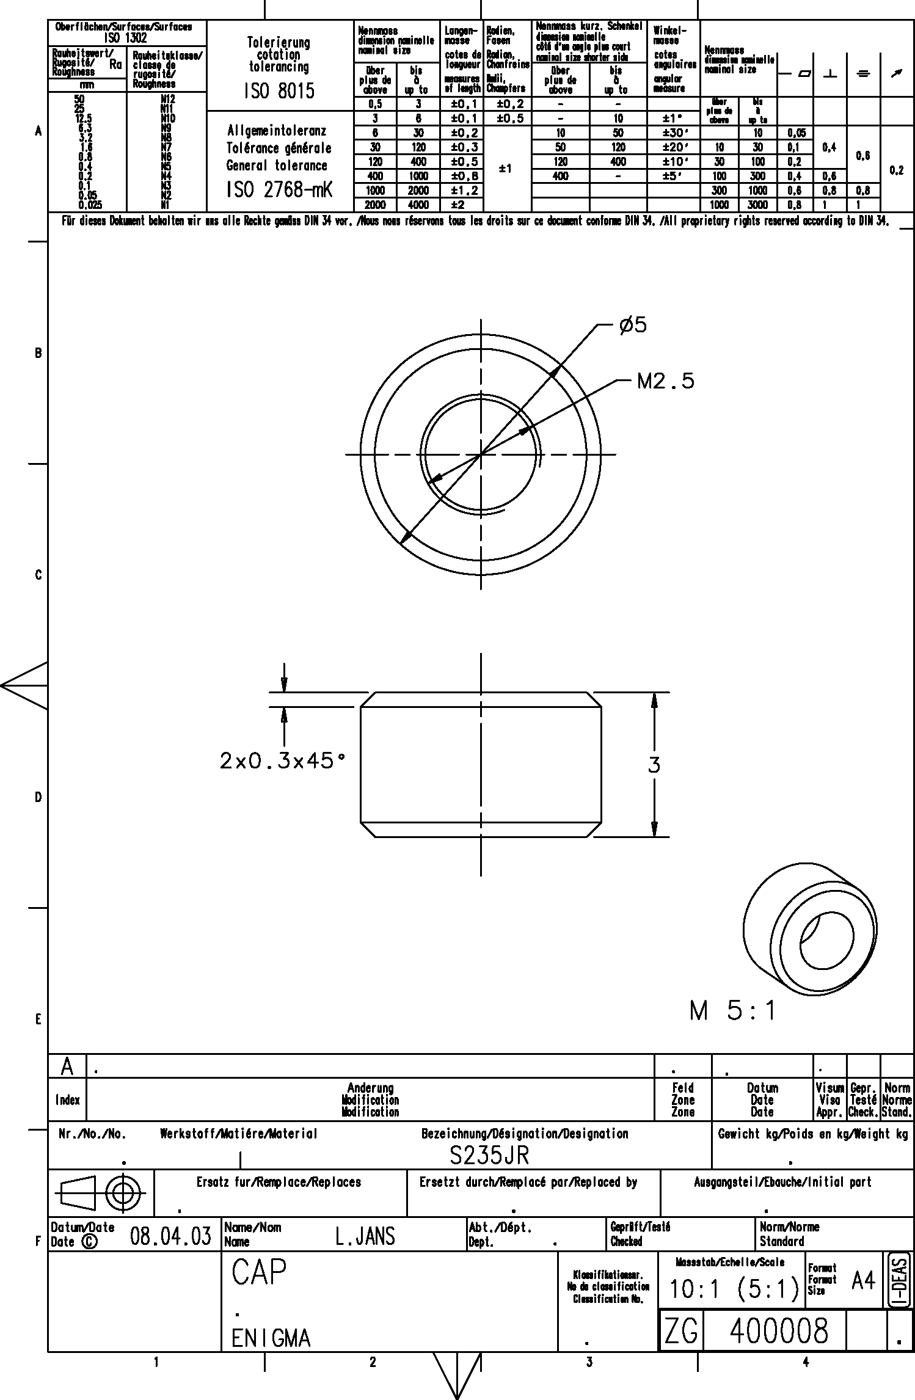
[picture p88: rotors/400008/BP.png]
