AresValley/ENIGMA/rotors/400015/README.md

<!-- PROJECT LOGO -->
<p align="center">
  <a href="https://github.com/AresValley/ENIGMA">
    
  </a>
</p>

<!-- ABOUT THE PROJECT -->
## COPING - 400 015

**ID:** 400015 <br/>
**Material:** [PA6](https://github.com/AresValley/ENIGMA#pa6-) <br/>
**Weight:** 6.48 g <br/>
**A360:** https://a360.co/3PhDWQf <br/>

### Blueprint
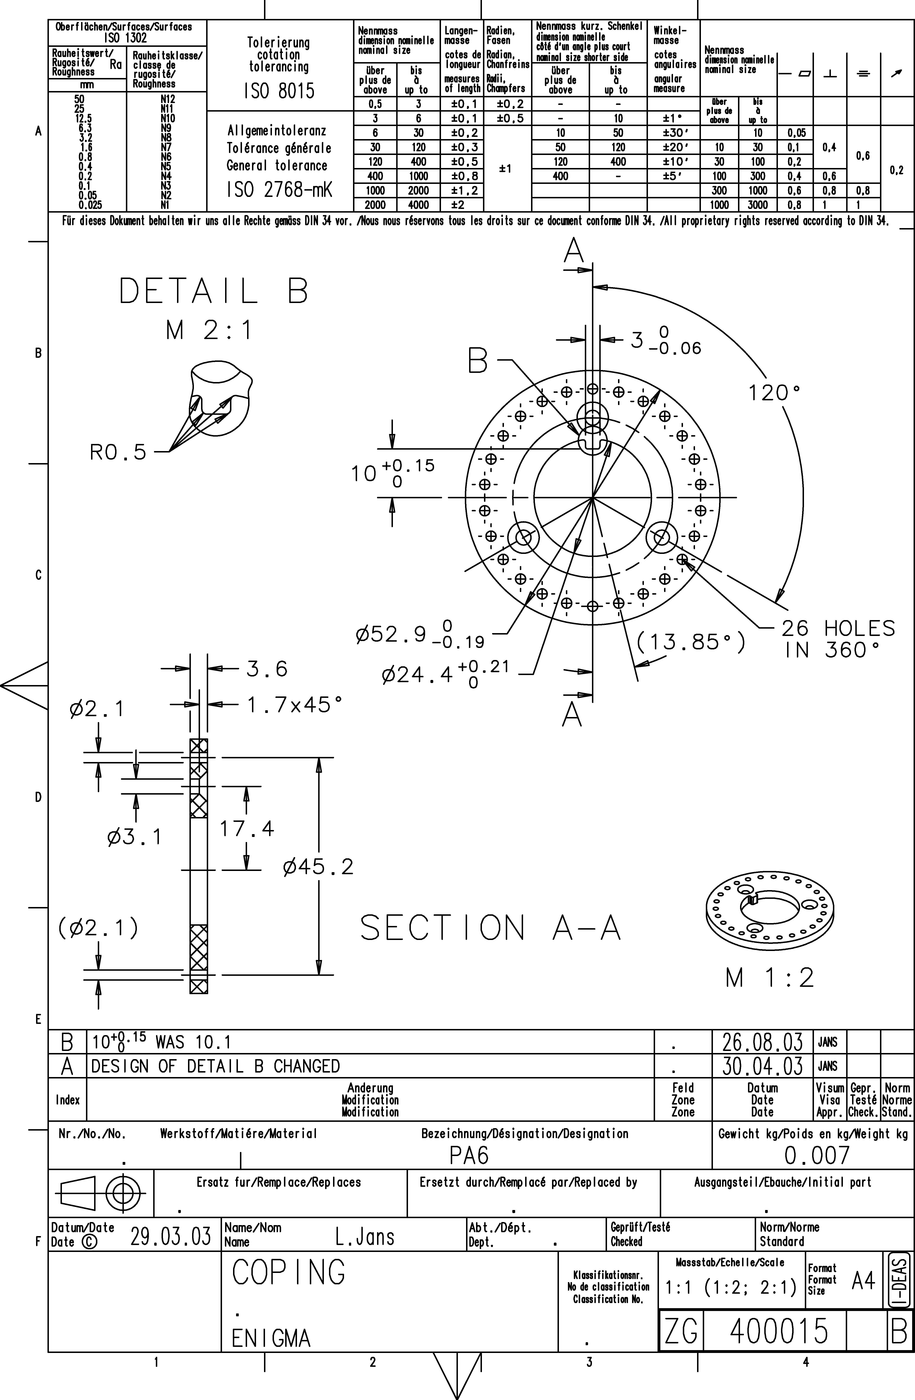
[picture p89: rotors/400015/BP.png]
