AresValley/ENIGMA/rotors/400010/README.md

<!-- PROJECT LOGO -->
<p align="center">
  <a href="https://github.com/AresValley/ENIGMA">
    
  </a>
</p>

<!-- ABOUT THE PROJECT -->
## Contact Die - 400 010

**ID:** 400010 <br/>
**Material:** [CuZn40](https://github.com/AresValley/ENIGMA#cuzn40-) <br/>
**Weight:** 0.145 g <br/>
**A360:** https://a360.co/3RkbmjU <br/>

### Blueprint
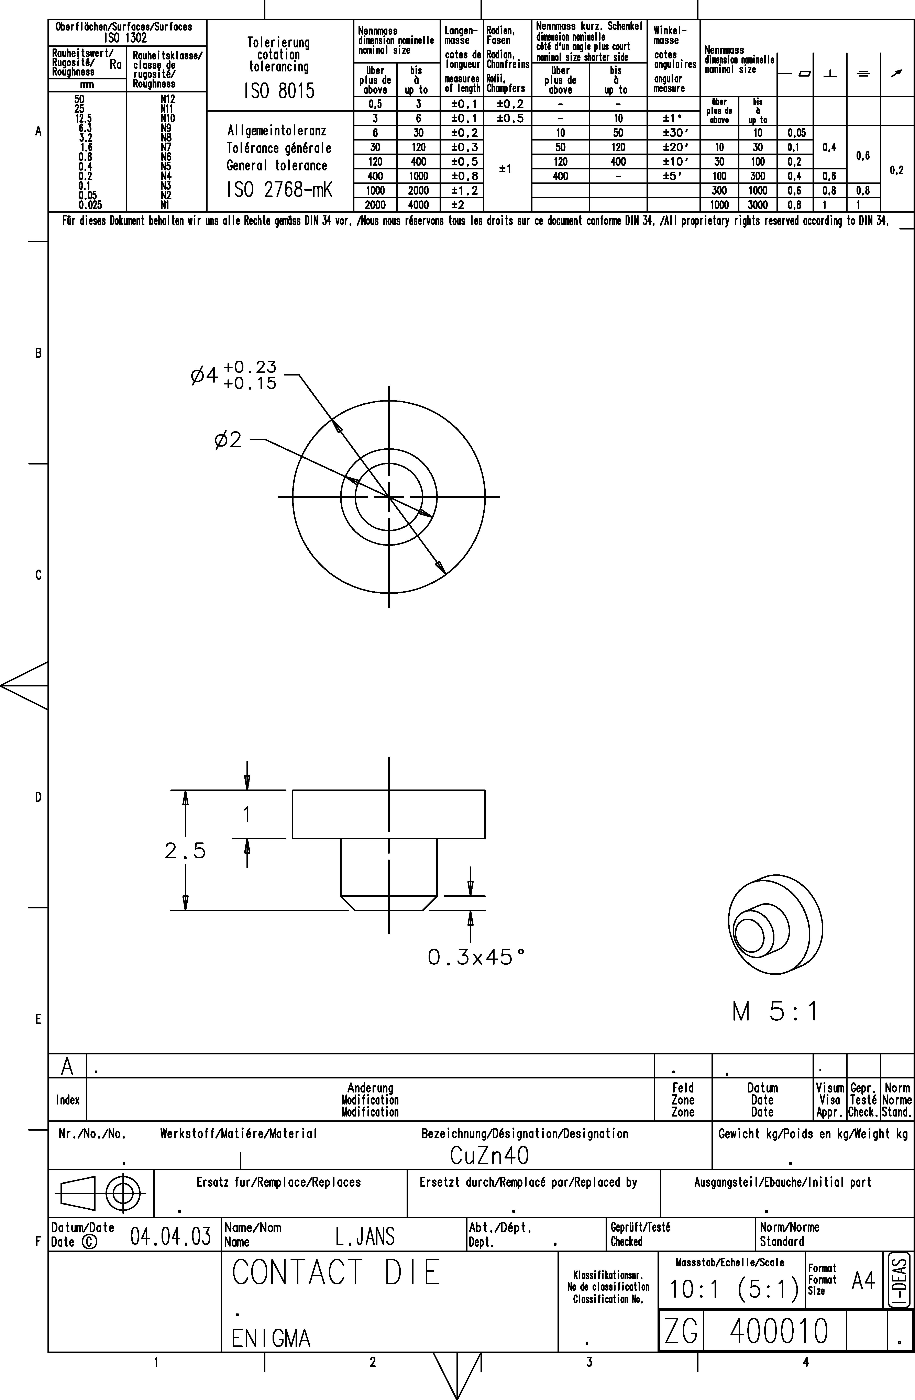
[picture p90: rotors/400010/BP.png]
Blueprint
