AresValley/ENIGMA/reflector/300001/README.md

<!-- PROJECT LOGO -->
<p align="center">
  <a href="https://github.com/AresValley/ENIGMA">
    
  </a>
</p>

<!-- ABOUT THE PROJECT -->
## REVERSE ROLL - 300 001

**ID:** 300001 <br/>
**Material:** [PA6](https://github.com/AresValley/ENIGMA#pa6) <br/>
**Weight:** 44.1 g <br/>
**A360:** https://a360.co/3R63lyF <br/>

### Blueprint
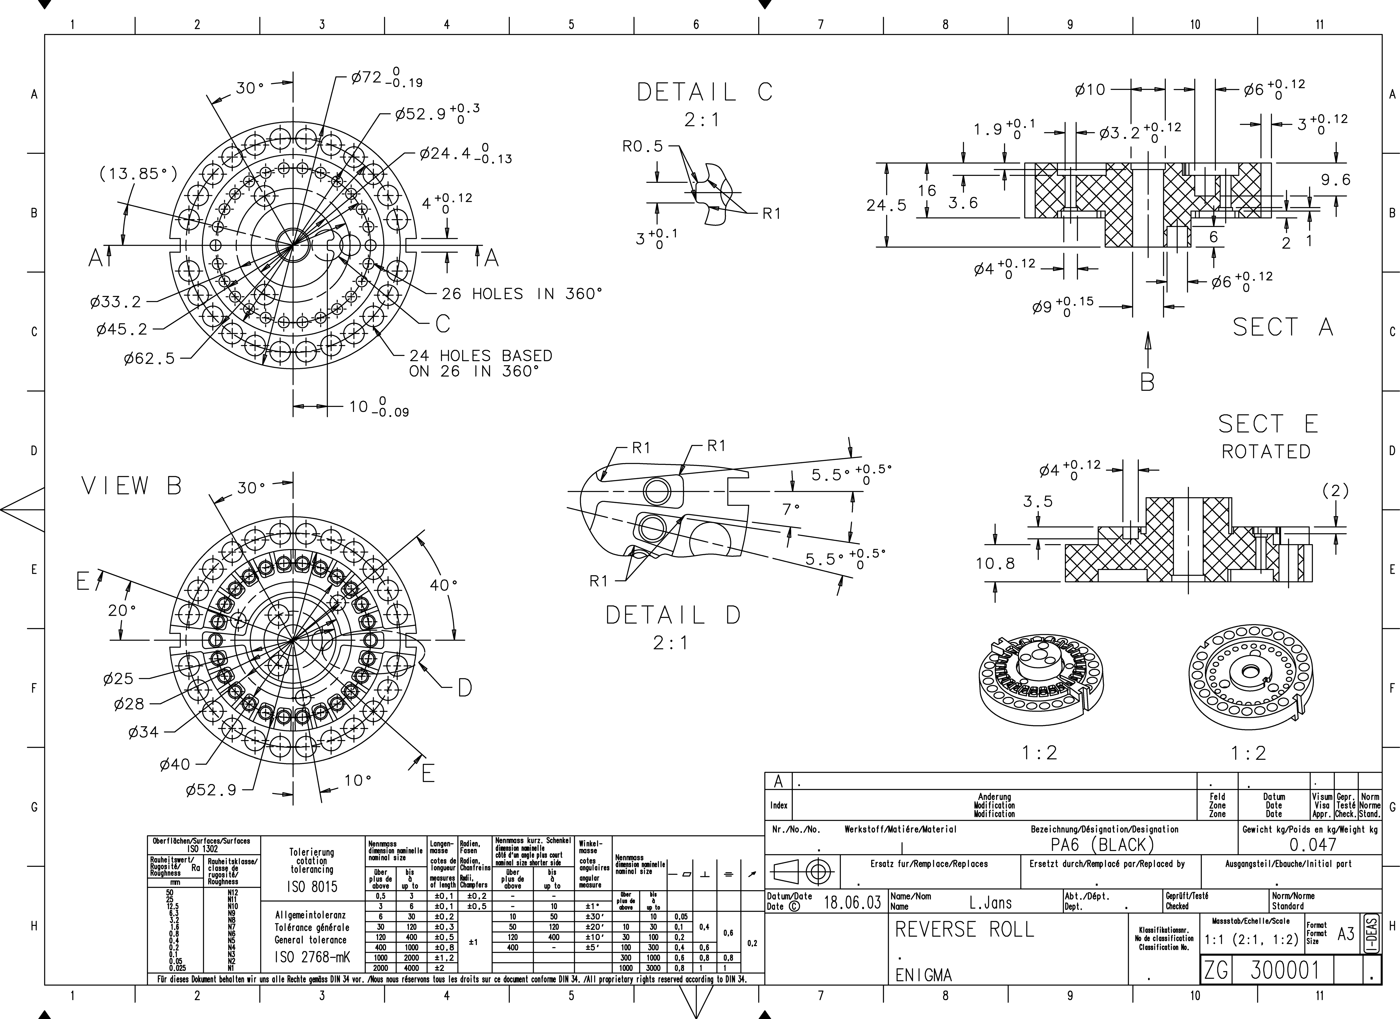
[picture p91: reflector/300001/BP.png]
Blueprint
