AresValley/ENIGMA/reflector/300002/README.md

<!-- PROJECT LOGO -->
<p align="center">
  <a href="https://github.com/AresValley/ENIGMA">
    
  </a>
</p>

<!-- ABOUT THE PROJECT -->
## CABINET - 300 002

**ID:** 300002 <br/>
**Material:** [S235JR](https://github.com/AresValley/ENIGMA#s235jr) <br/>
**Weight:** 136.4 g <br/>
**A360:** https://a360.co/3swAUzE <br/>

### Blueprint
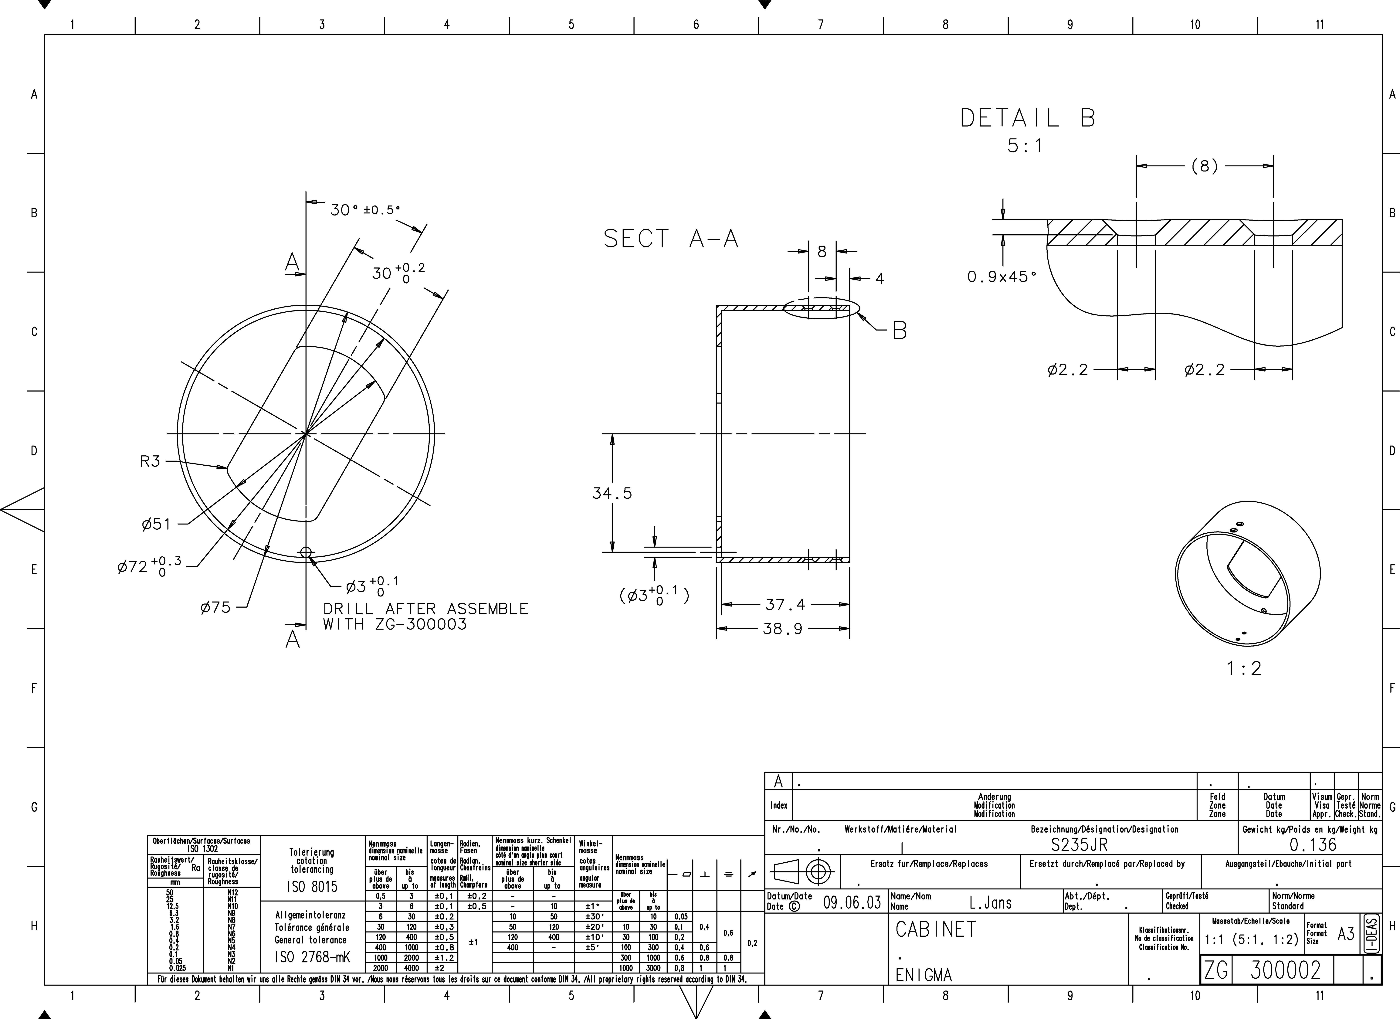
[picture p92: reflector/300002/BP.png]
Blueprint
