AresValley/ENIGMA/reflector/300003/README.md

<!-- PROJECT LOGO -->
<p align="center">
  <a href="https://github.com/AresValley/ENIGMA">
    
  </a>
</p>

<!-- ABOUT THE PROJECT -->
## WEDGE HOLDER - 300 003

**ID:** 300003 <br/>
**Material:** [S235JR](https://github.com/AresValley/ENIGMA#s235jr) <br/>
**Weight:** 52.3 g <br/>
**A360:** https://a360.co/3L3ollU <br/>

### Blueprint
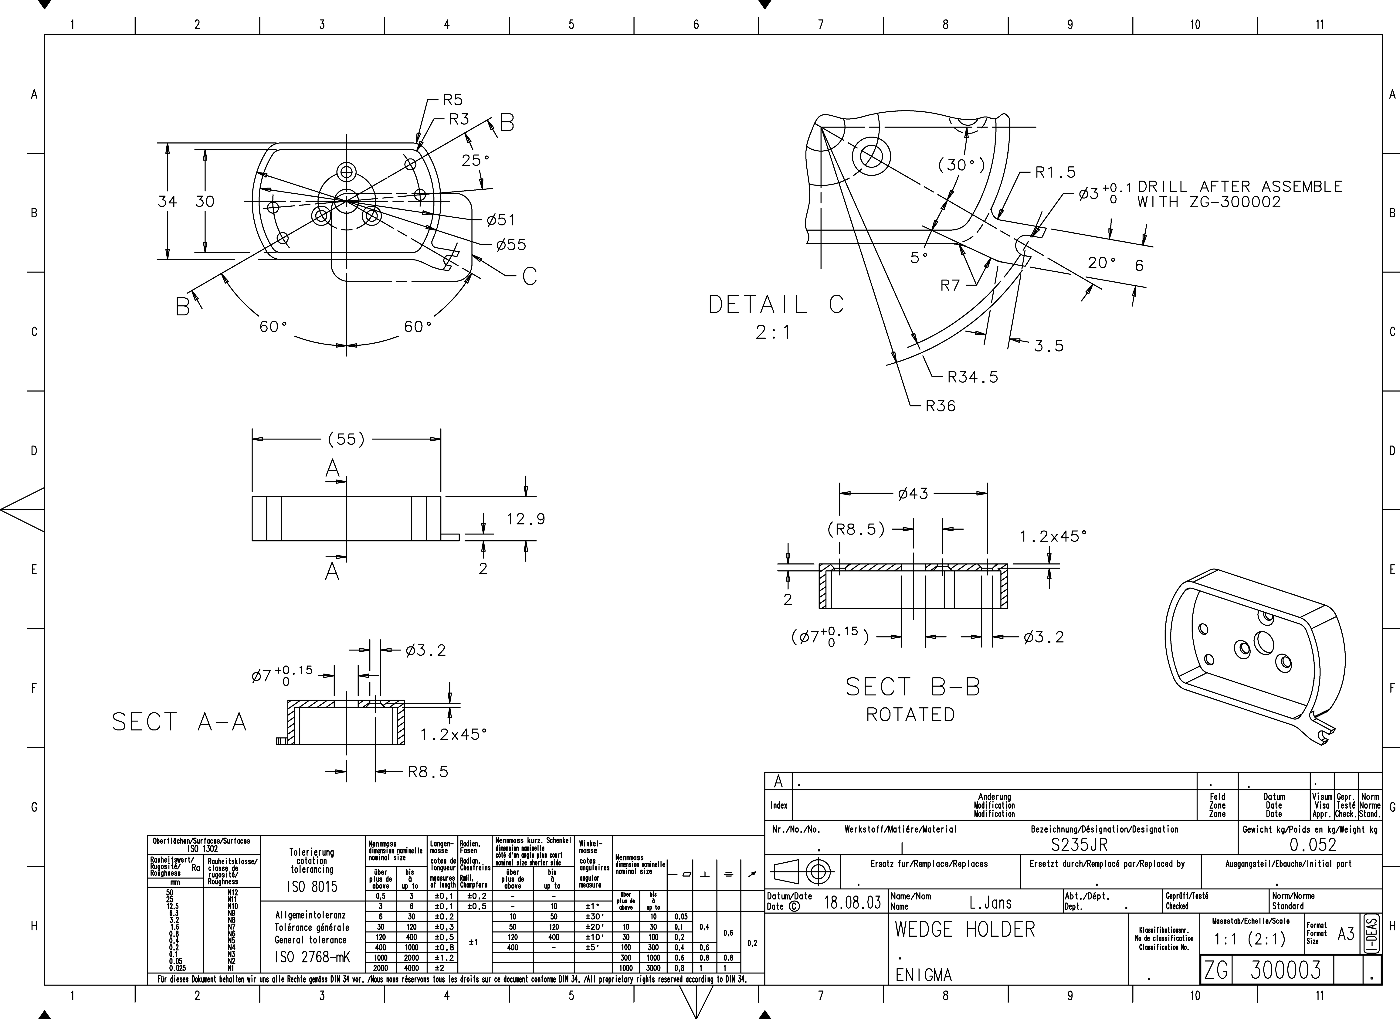
[picture p93: reflector/300003/BP.png]
Blueprint
