AresValley/ENIGMA/reflector/300005/README.md

<!-- PROJECT LOGO -->
<p align="center">
  <a href="https://github.com/AresValley/ENIGMA">
    
  </a>
</p>

<!-- ABOUT THE PROJECT -->
## BLANK - 300 005

**ID:** 300005 <br/>
**Material:** [CuZn40](https://github.com/AresValley/ENIGMA#cuzn40) <br/>
**Weight:** 0.3 g <br/>
**A360:** https://a360.co/44qnyT3 <br/>

### Blueprint
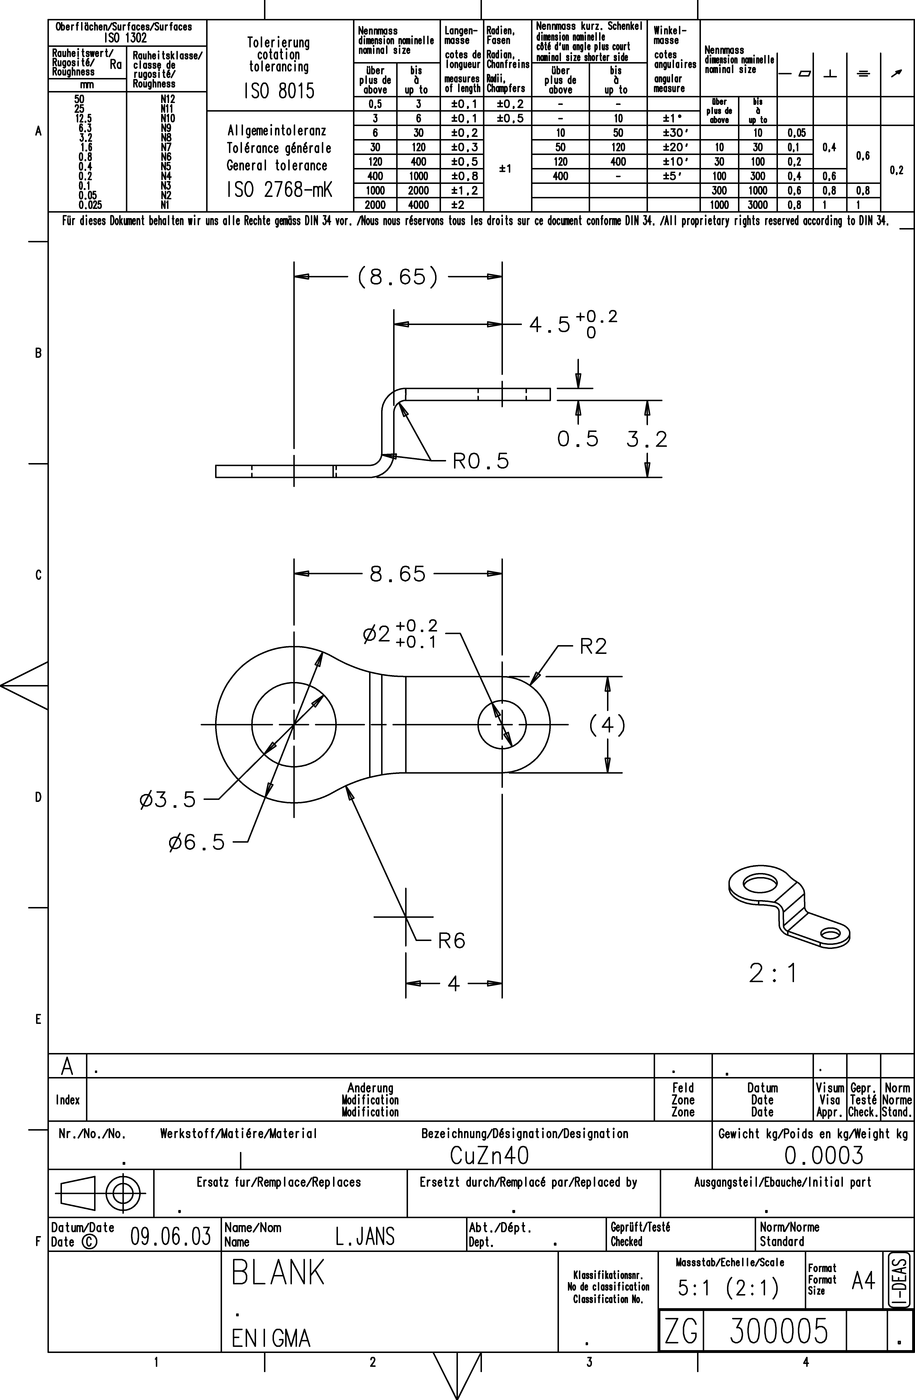
[picture p94: reflector/300005/BP.png]
Blueprint
