AresValley/ENIGMA/reflector/300004/README.md

<!-- PROJECT LOGO -->
<p align="center">
  <a href="https://github.com/AresValley/ENIGMA">
    
  </a>
</p>

<!-- ABOUT THE PROJECT -->
## WEDGE - 300 004

**ID:** 300004 <br/>
**Material:** [S235JR](https://github.com/AresValley/ENIGMA#s235jr) <br/>
**Weight:** 9.6 g <br/>
**A360:** https://a360.co/3OU3Ysp <br/>

### Blueprint
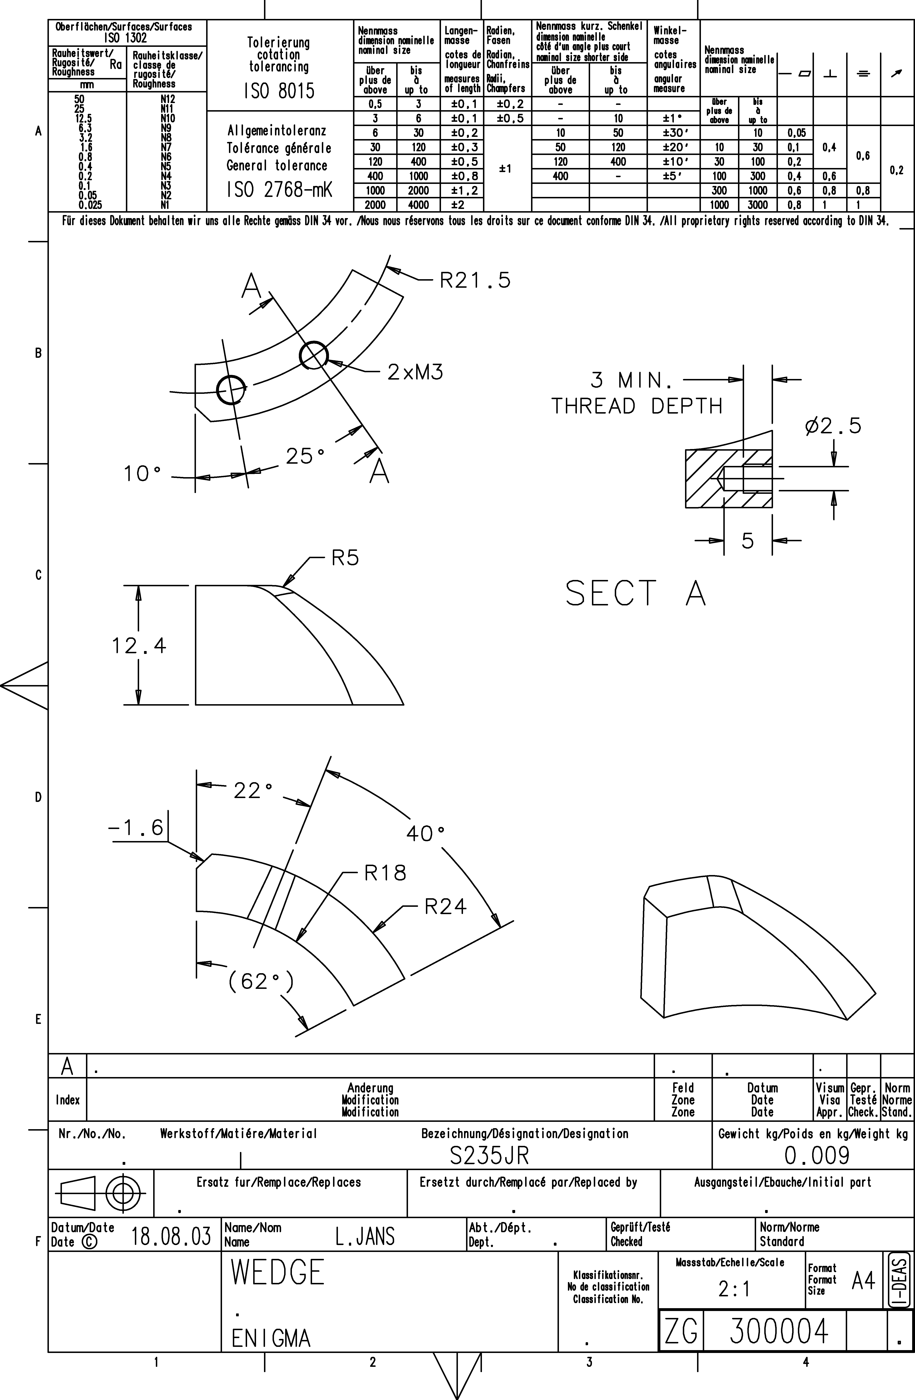
[picture p95: reflector/300004/BP.png]
Blueprint
