AresValley/ENIGMA/rotors/400202.png

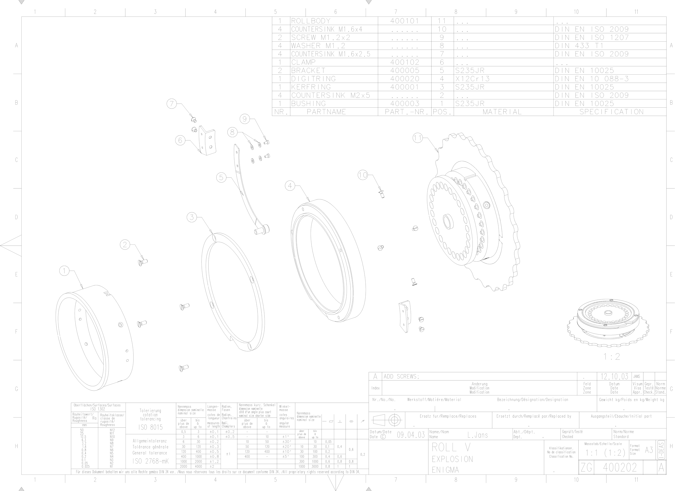
rotors/400202.png
