AresValley/ENIGMA/rotors/400203.png

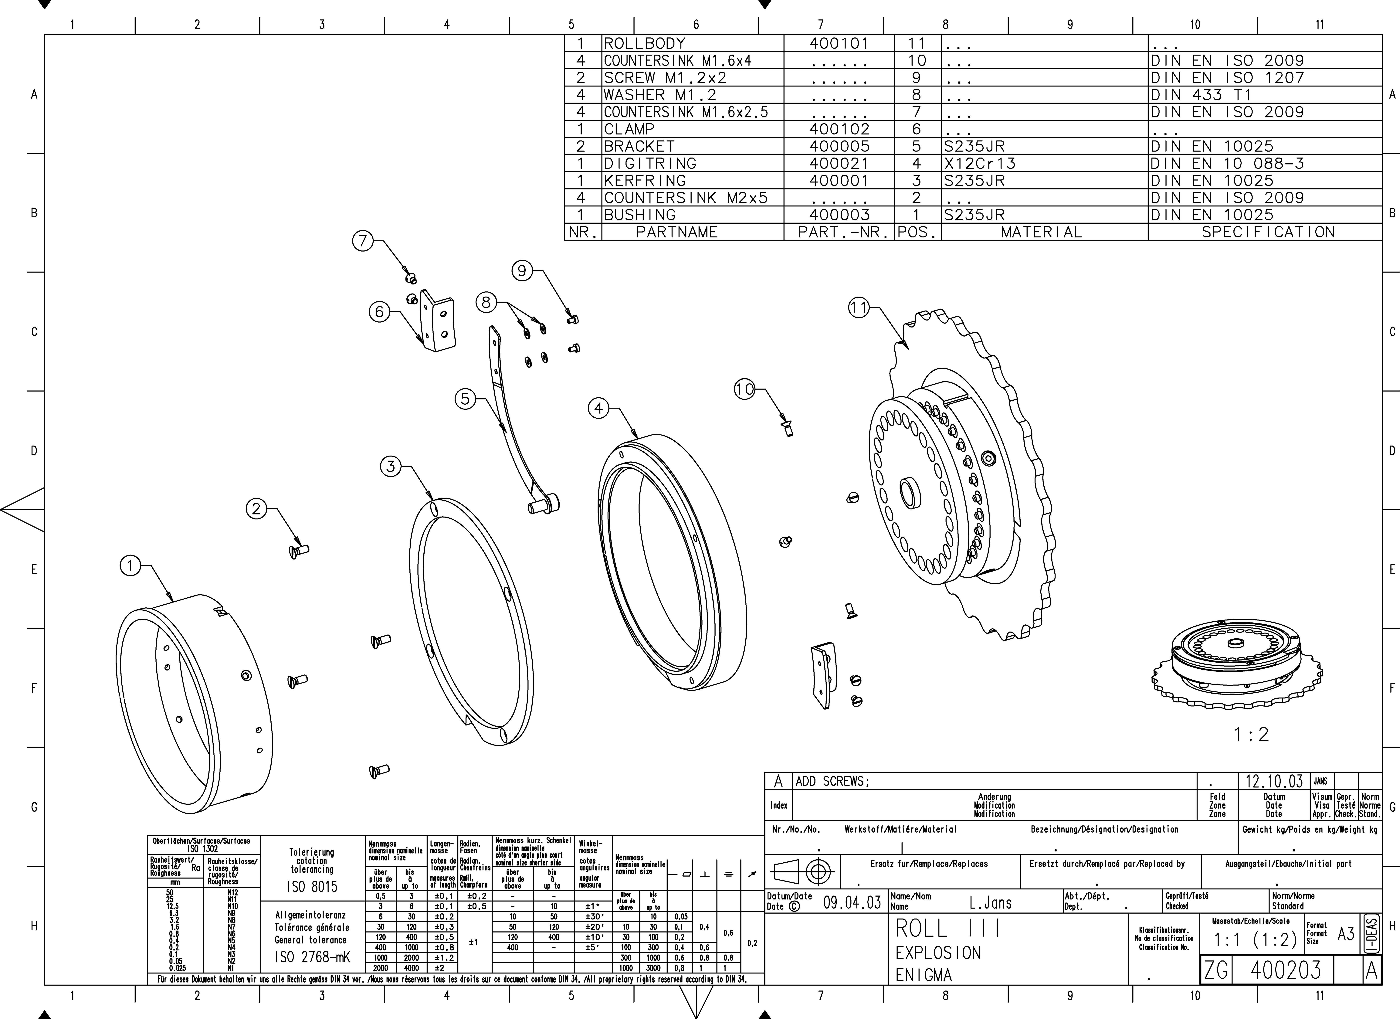
rotors/400203.png
