AresValley/ENIGMA/rack/100051/100051.3mf

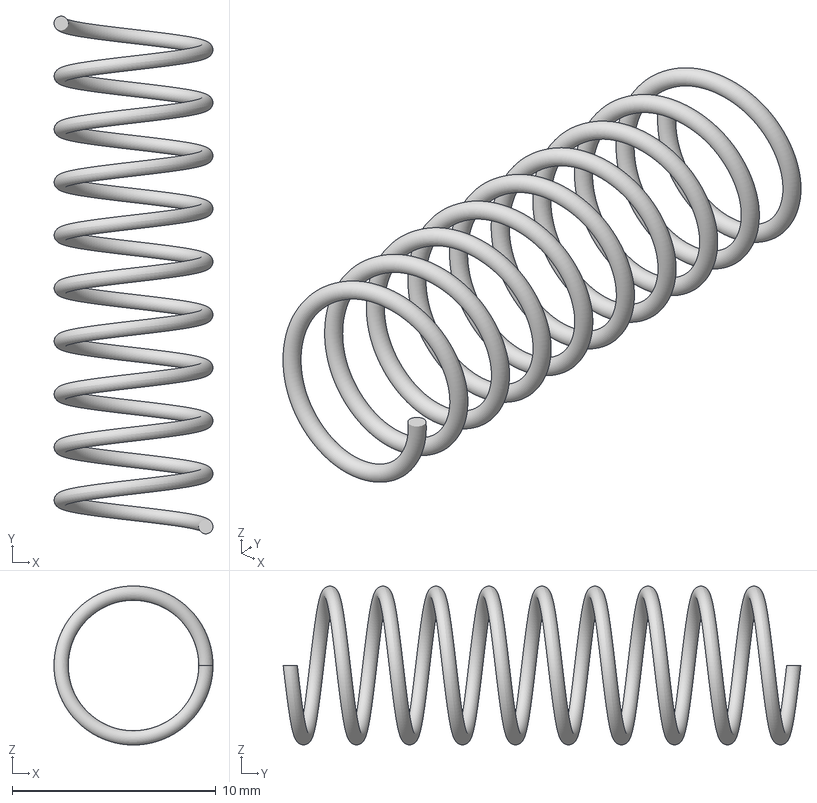
[picture p112: CAD file, 2024-11-22]
rack/100051/100051.3mf
7.80 x 25.4 x 7.80 mm
