AresValley/ENIGMA/rack/100052/100052.3mf

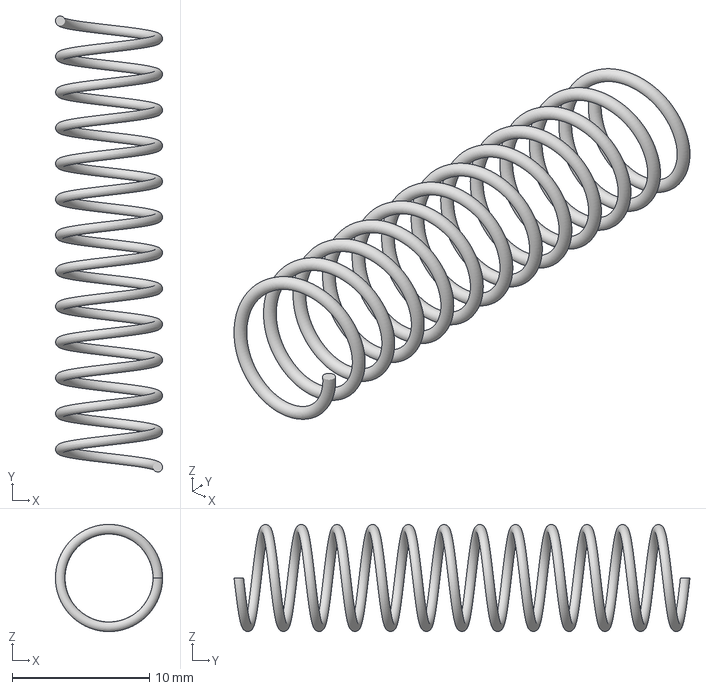
[picture p113: CAD file, 2024-11-20]
rack/100052/100052.3mf
7.80 x 33.2 x 7.80 mm
