AresValley/ENIGMA/rack/100054/100054.3mf

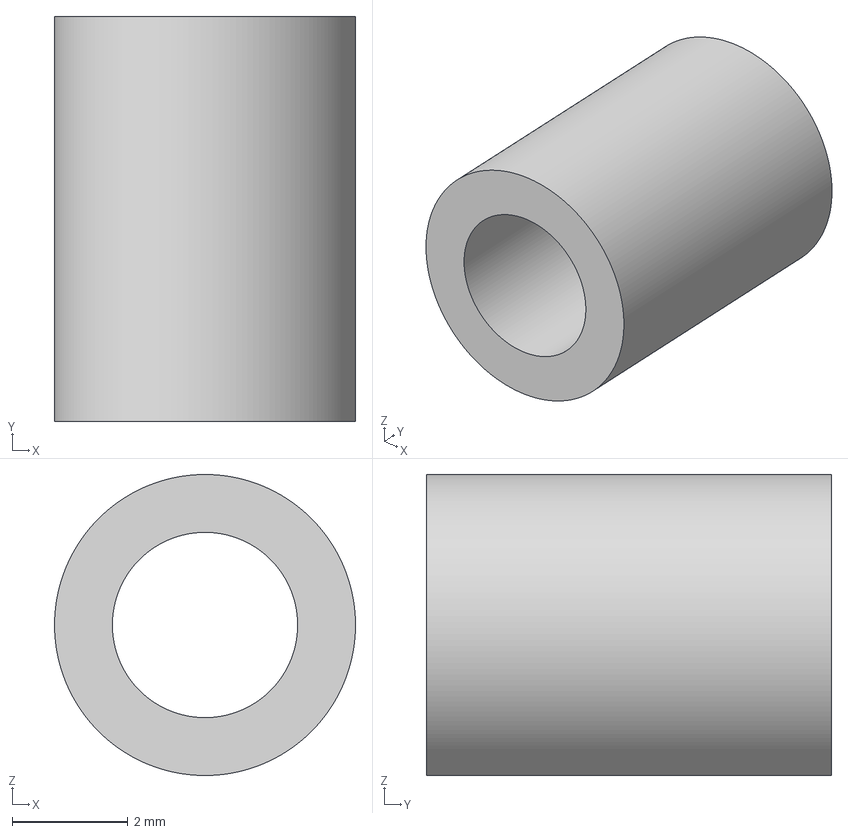
[picture p114: CAD file, 2024-11-22]
rack/100054/100054.3mf
5.20 x 7.00 x 5.20 mm
