AresValley/ENIGMA/reflector/300001/300001.3mf

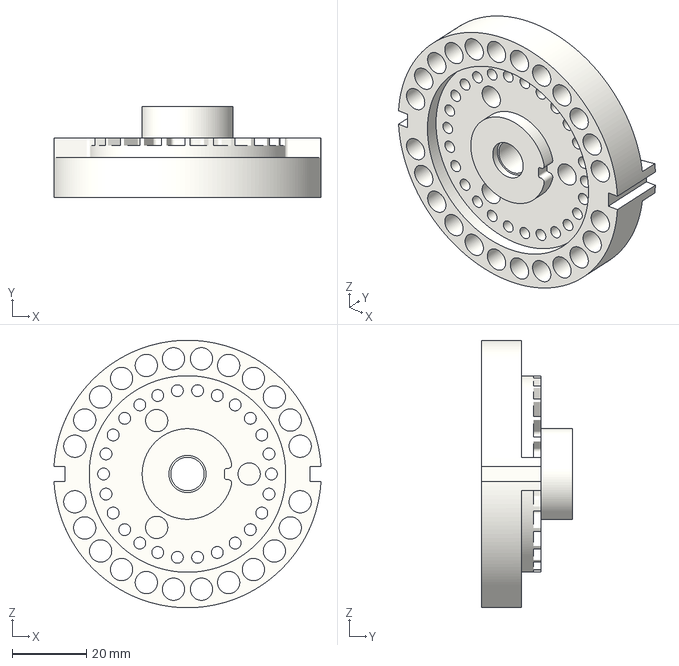
[picture p115: CAD file, 2023-09-02]
reflector/300001/300001.3mf
71.9 x 24.5 x 72.0 mm
